varjagg/digital-modul-m/images/350d_full_cycle_original.png

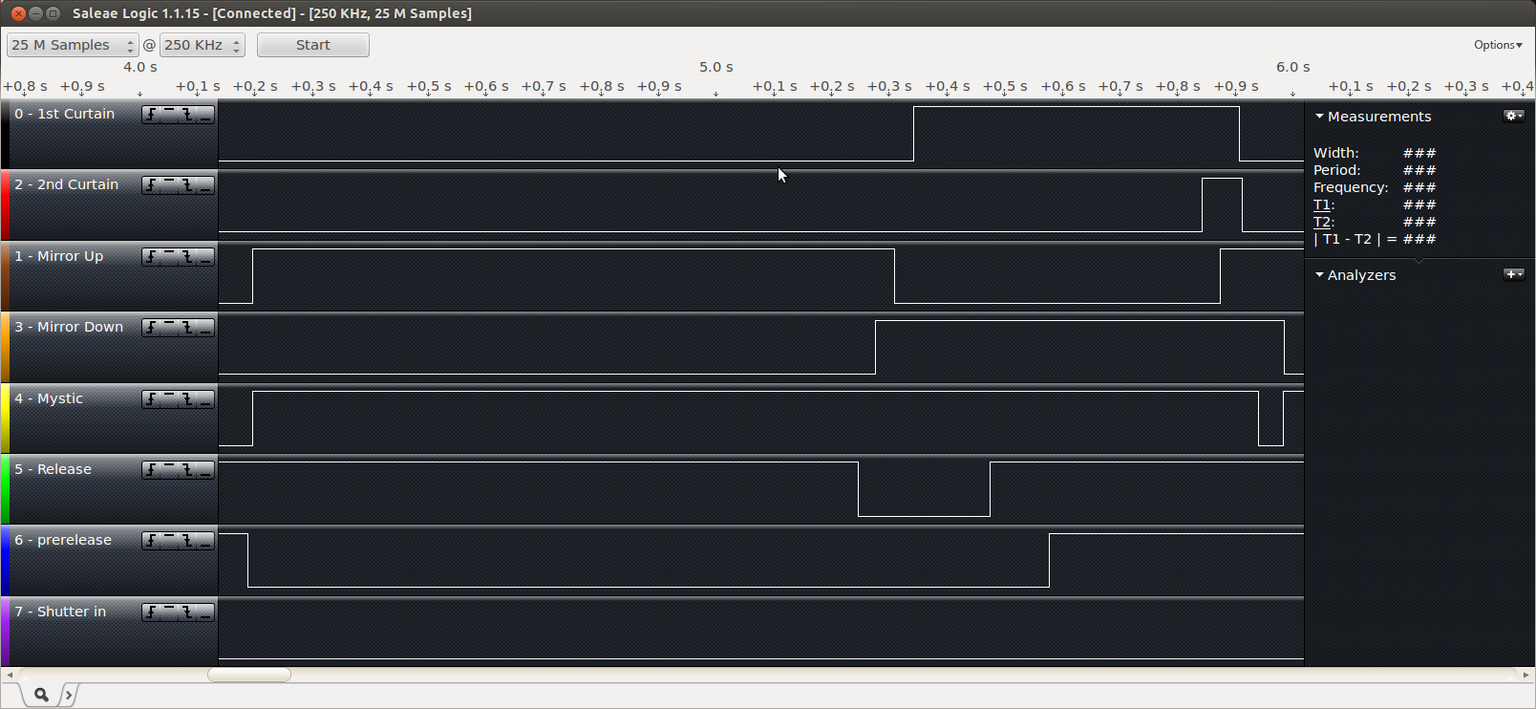
images/350d_full_cycle_original.png
