varjagg/digital-modul-m/images/actuation_uc_side.png

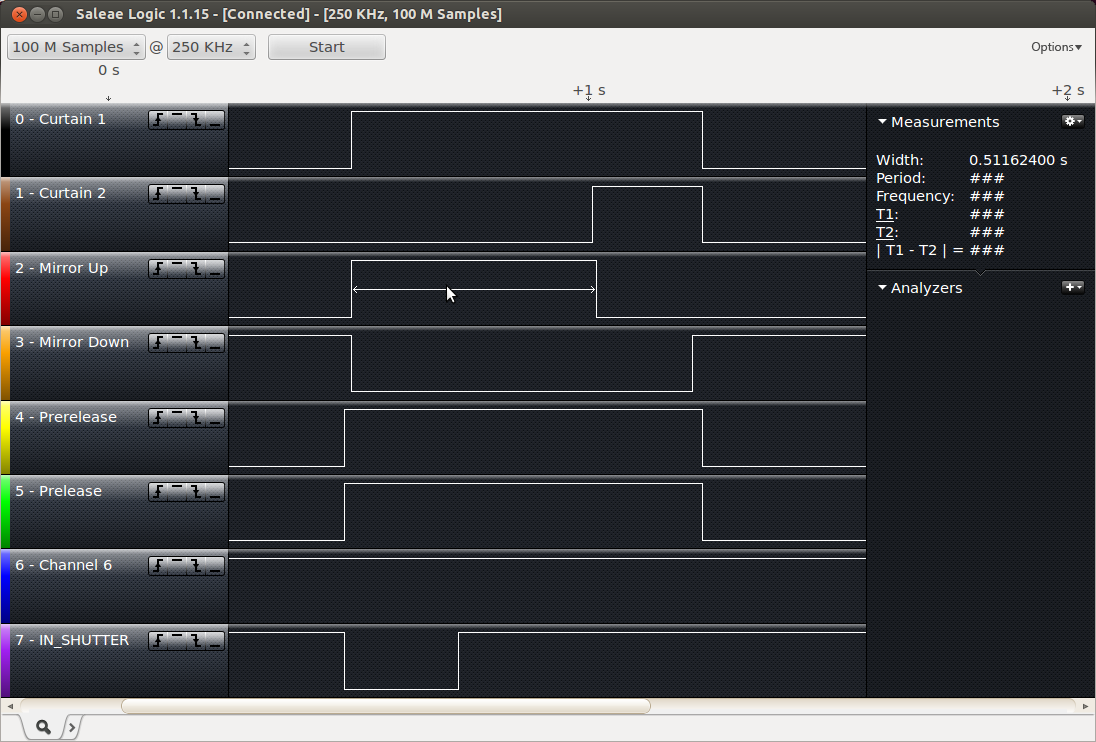
images/actuation_uc_side.png
