varjagg/digital-modul-m/images/assy/2013-04-25 13.25.53.jpg

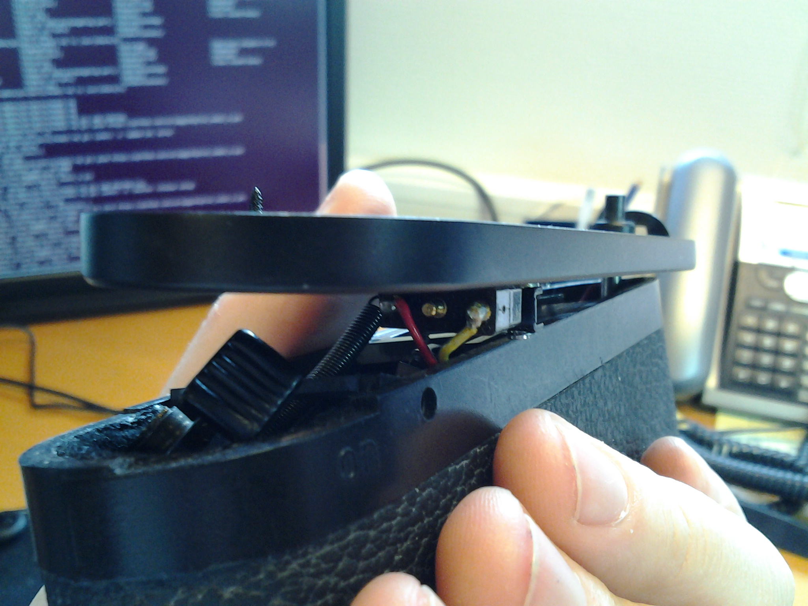
images/assy/2013-04-25 13.25.53.jpg
