varjagg/digital-modul-m/images/assy/2013-04-25 13.26.48.jpg

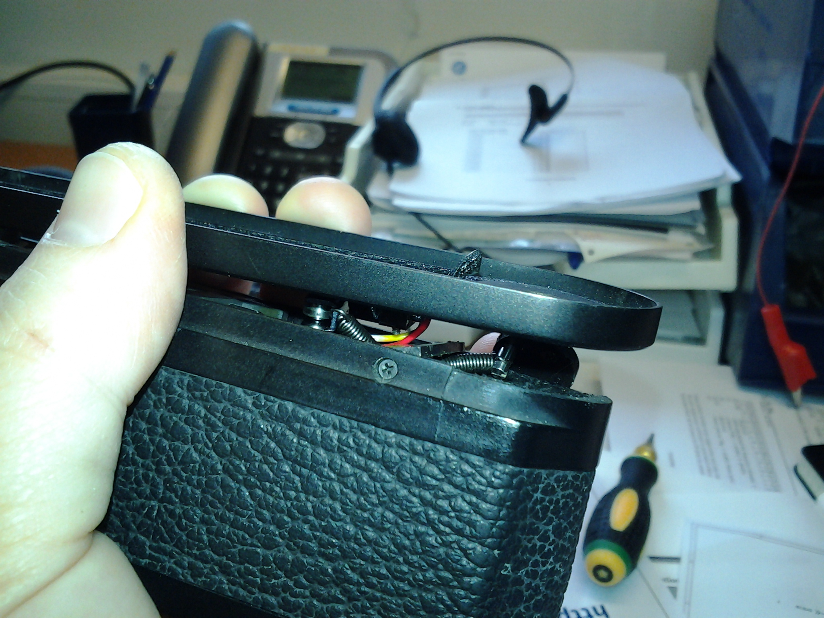
images/assy/2013-04-25 13.26.48.jpg
