varjagg/digital-modul-m/images/assy/2013-04-25 13.37.47.jpg

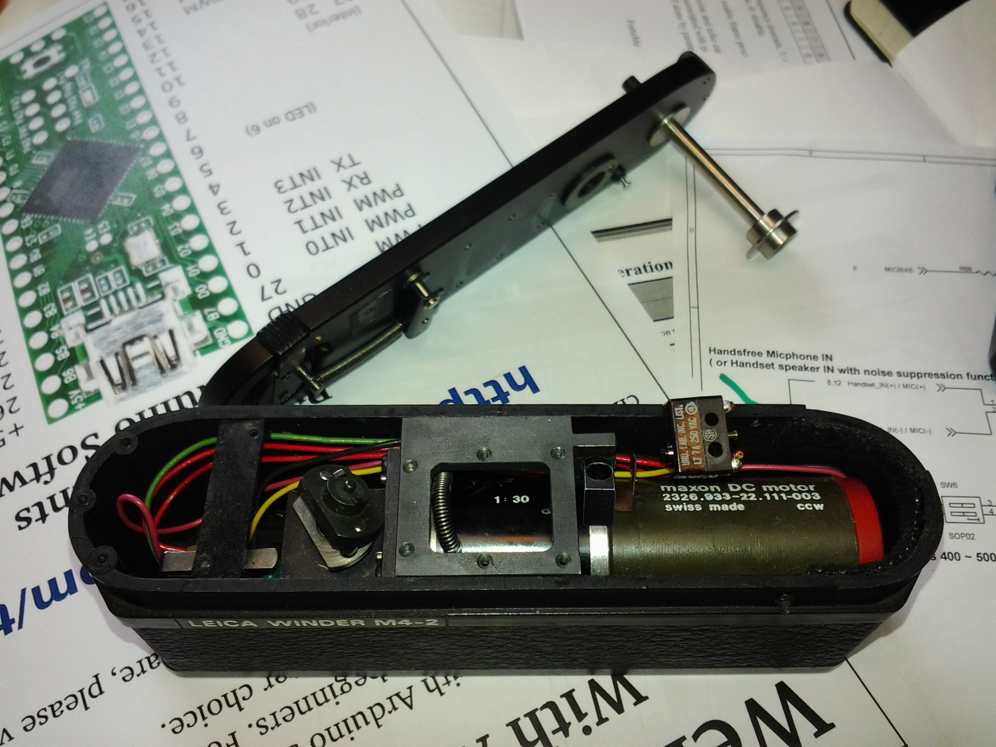
images/assy/2013-04-25 13.37.47.jpg
