varjagg/digital-modul-m/images/assy/2013-04-25 15.04.17.jpg

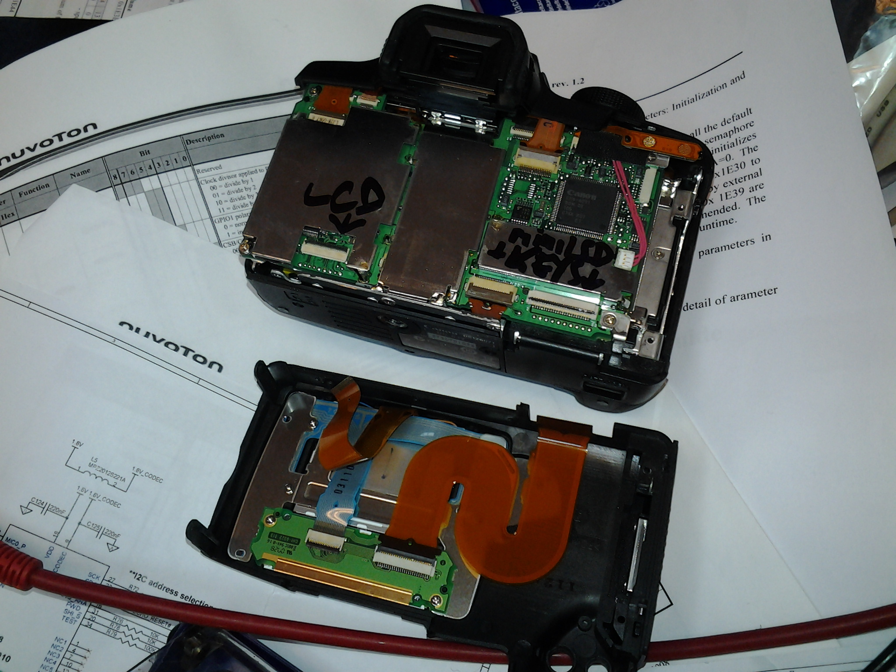
images/assy/2013-04-25 15.04.17.jpg
