varjagg/digital-modul-m/images/assy/2013-04-26 10.56.45.jpg

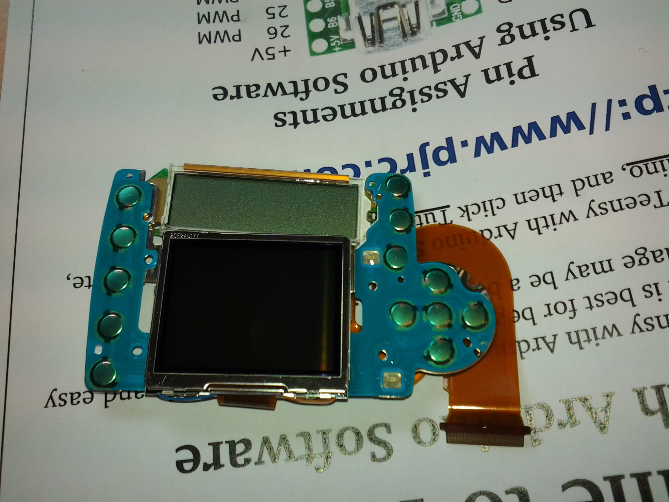
images/assy/2013-04-26 10.56.45.jpg
