varjagg/digital-modul-m/images/assy/2013-04-26 14.56.13.jpg

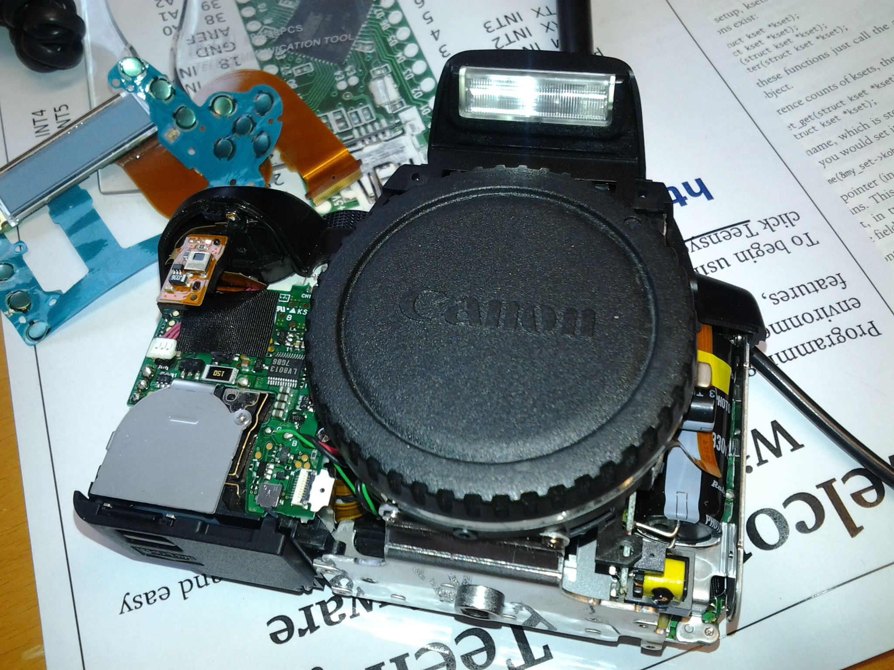
images/assy/2013-04-26 14.56.13.jpg
