varjagg/digital-modul-m/images/assy/2013-04-30 14.38.24.jpg

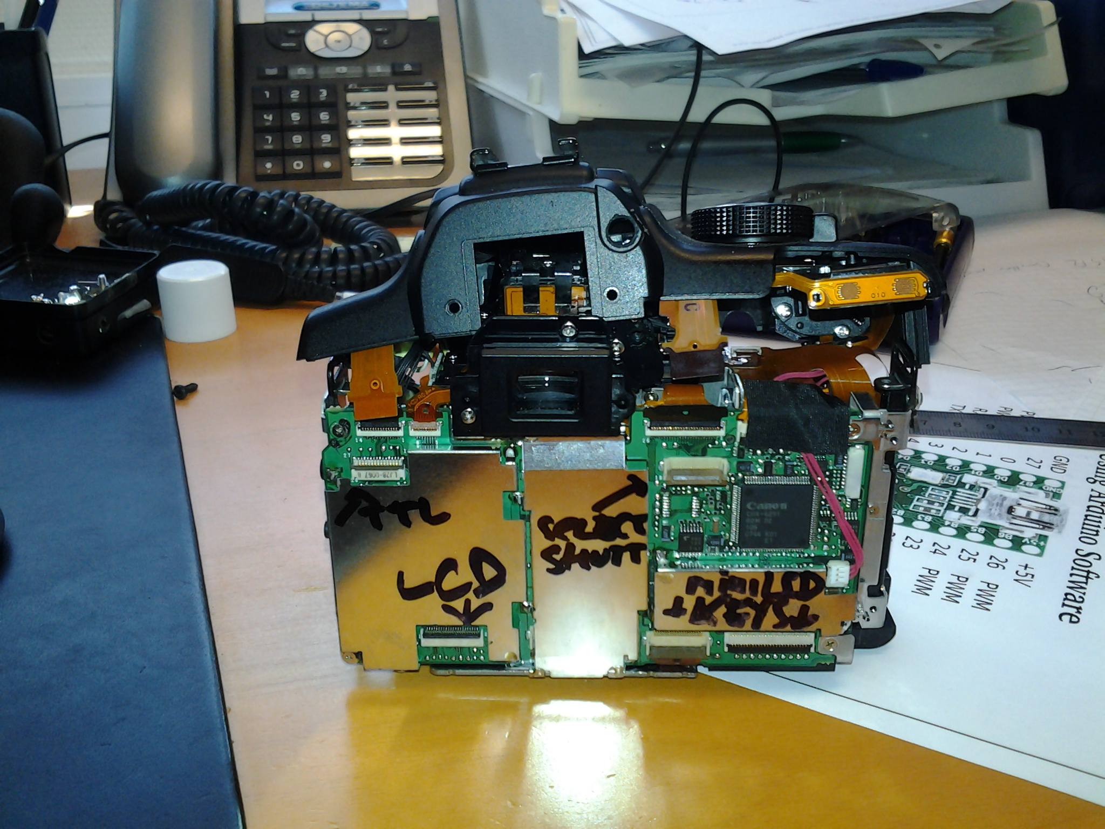
images/assy/2013-04-30 14.38.24.jpg
