varjagg/digital-modul-m/images/assy/2013-04-30 14.41.12.jpg

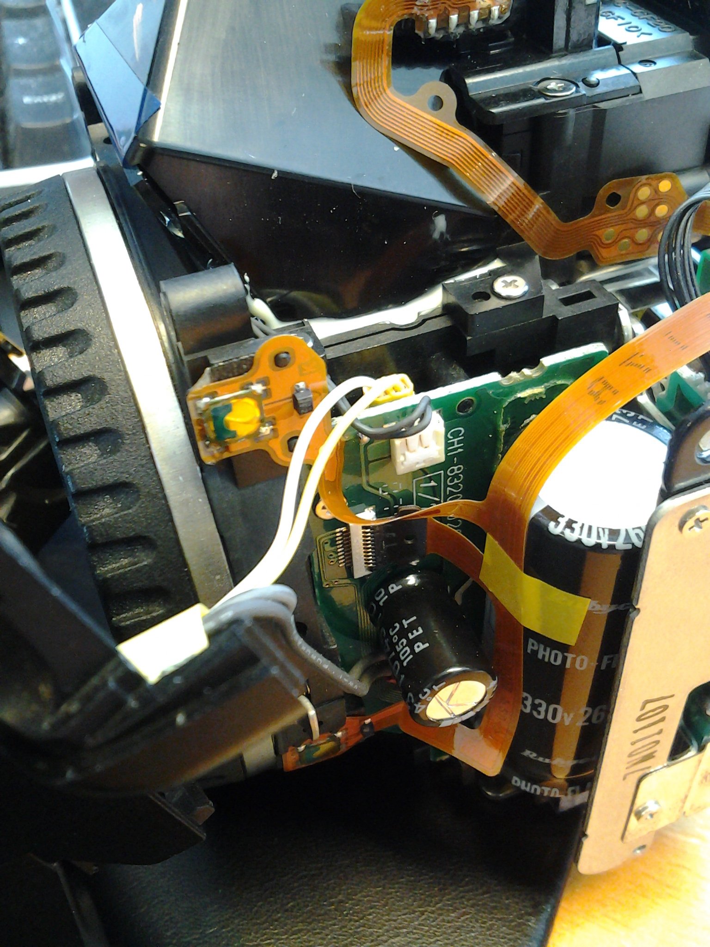
images/assy/2013-04-30 14.41.12.jpg
