varjagg/digital-modul-m/images/assy/2013-04-30 15.58.13.jpg

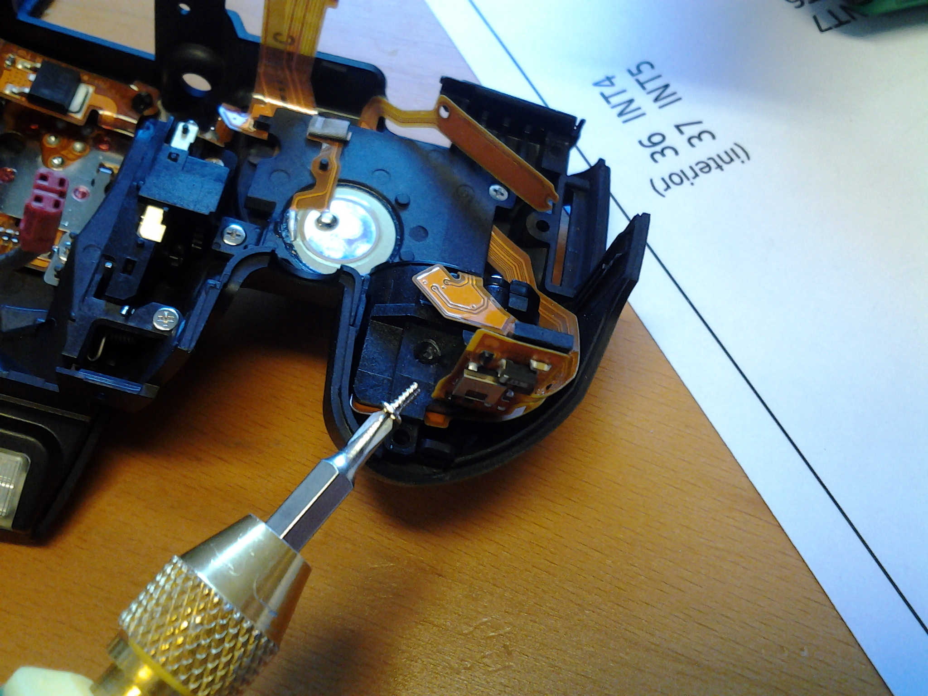
images/assy/2013-04-30 15.58.13.jpg
