varjagg/digital-modul-m/images/assy/2013-04-30 16.00.38.jpg

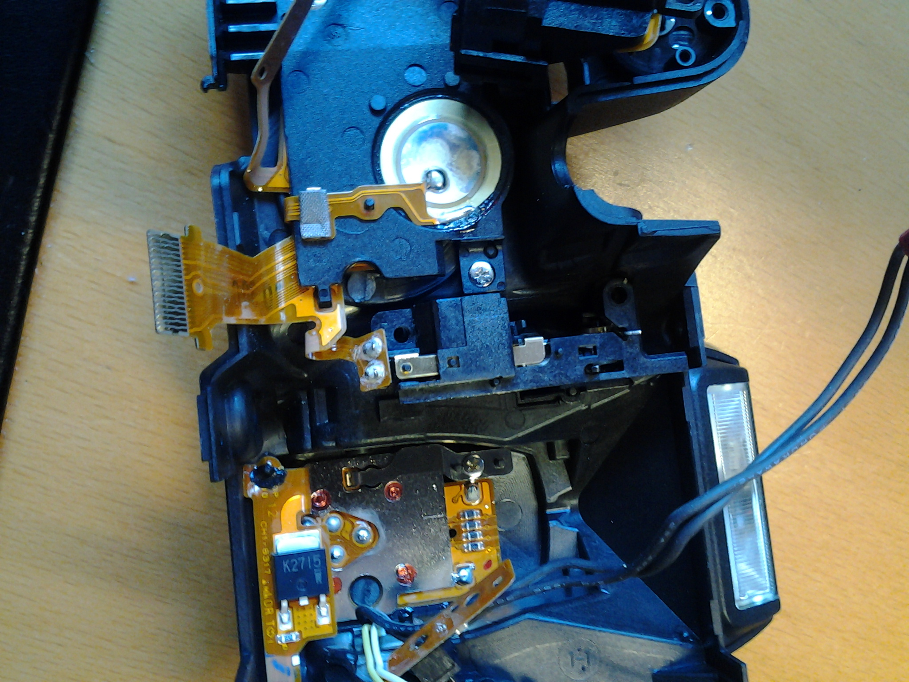
images/assy/2013-04-30 16.00.38.jpg
