varjagg/digital-modul-m/images/assy/2013-05-02 13.31.28.jpg

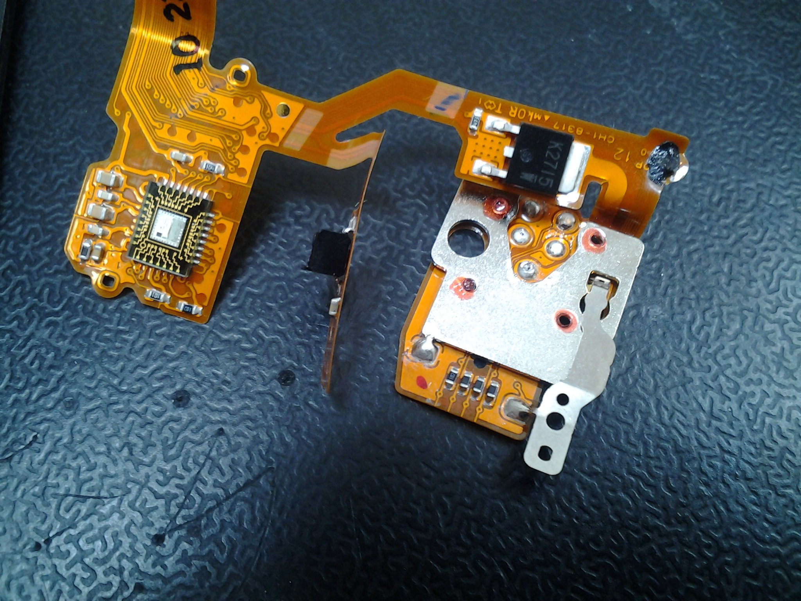
images/assy/2013-05-02 13.31.28.jpg
