varjagg/digital-modul-m/images/assy/2013-05-03 12.45.25.jpg

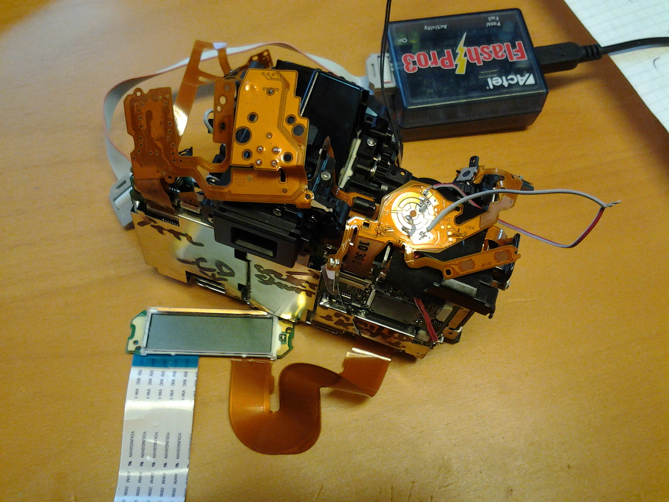
images/assy/2013-05-03 12.45.25.jpg
