varjagg/digital-modul-m/images/assy/2013-05-06 17.41.58.jpg

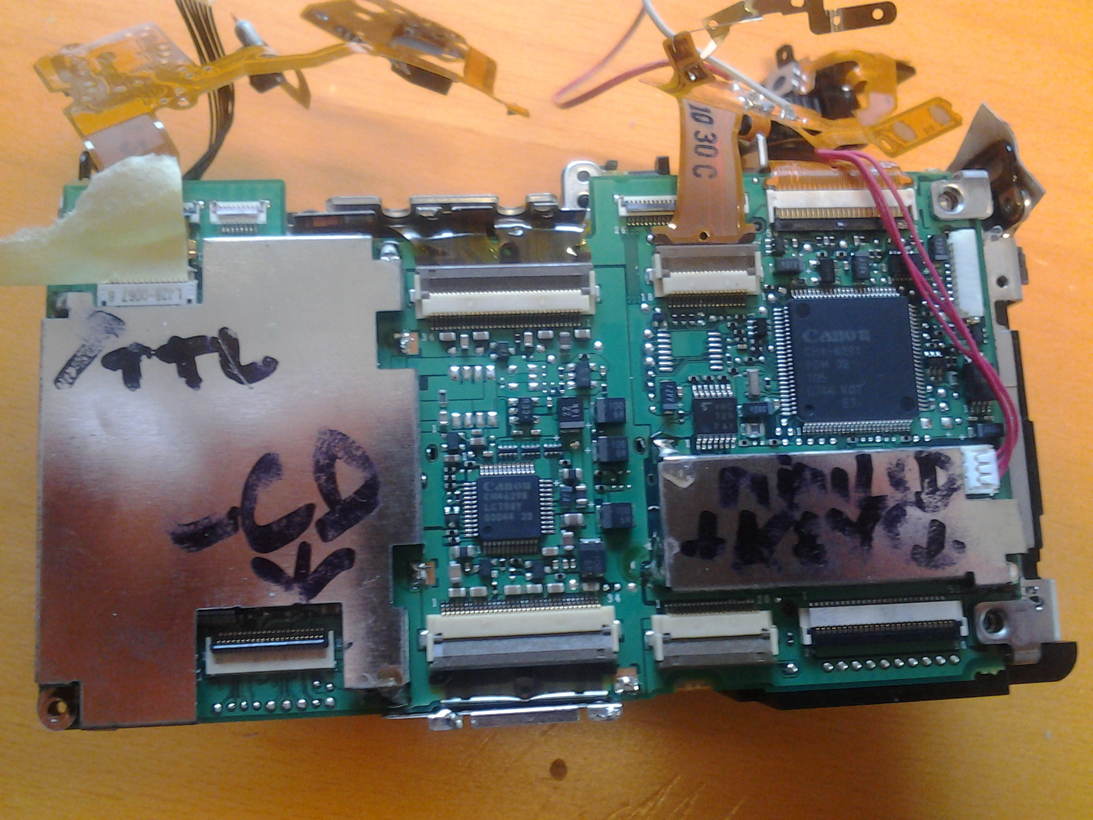
images/assy/2013-05-06 17.41.58.jpg
