varjagg/digital-modul-m/images/assy/2013-05-06 17.49.36.jpg

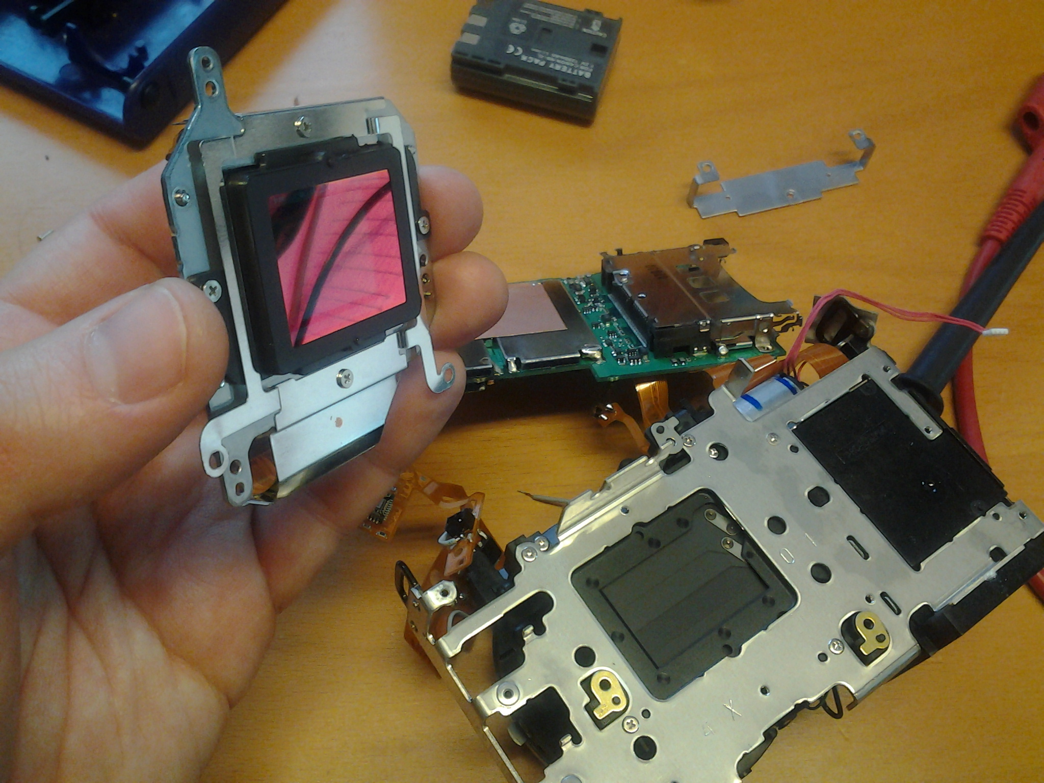
images/assy/2013-05-06 17.49.36.jpg
