varjagg/digital-modul-m/images/assy/2013-05-07 17.15.51.jpg

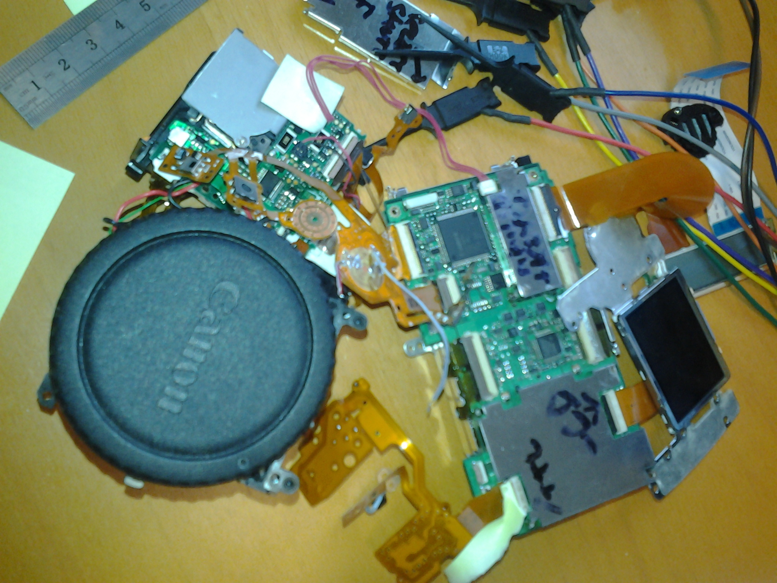
images/assy/2013-05-07 17.15.51.jpg
