varjagg/digital-modul-m/images/assy/2013-12-18 17.05.55.jpg

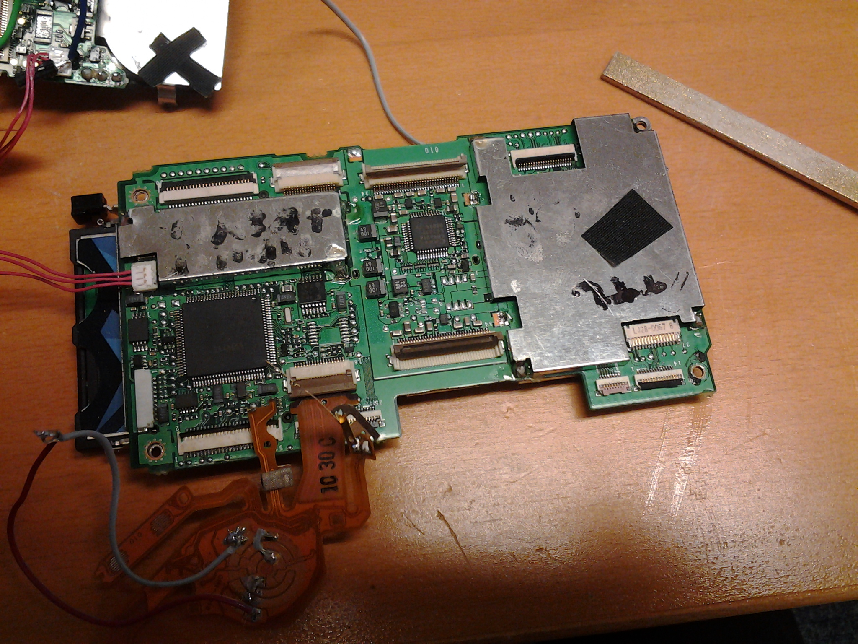
images/assy/2013-12-18 17.05.55.jpg
