varjagg/digital-modul-m/images/assy/2013-12-19 19.09.14.jpg

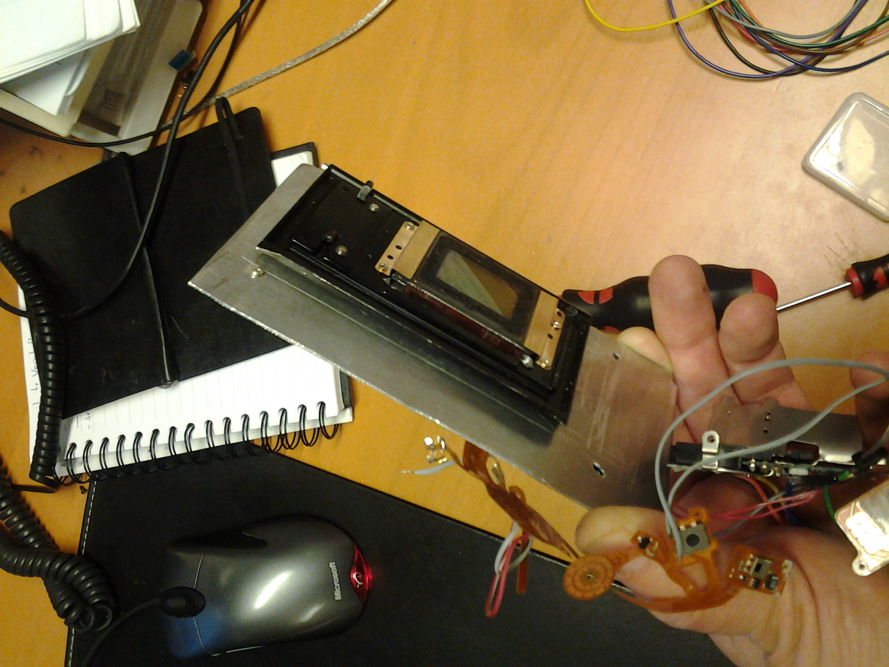
images/assy/2013-12-19 19.09.14.jpg
