varjagg/digital-modul-m/images/assy/2013-12-20 17.21.03.jpg

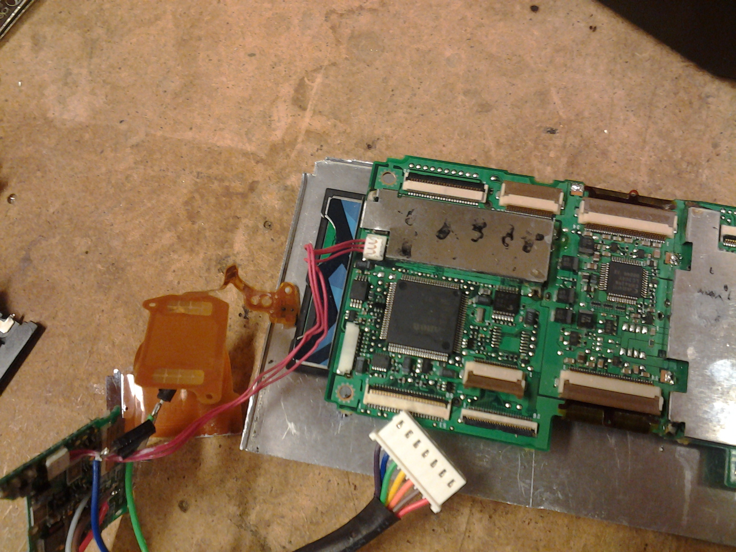
images/assy/2013-12-20 17.21.03.jpg
