varjagg/digital-modul-m/images/assy/2013-12-20 17.26.51.jpg

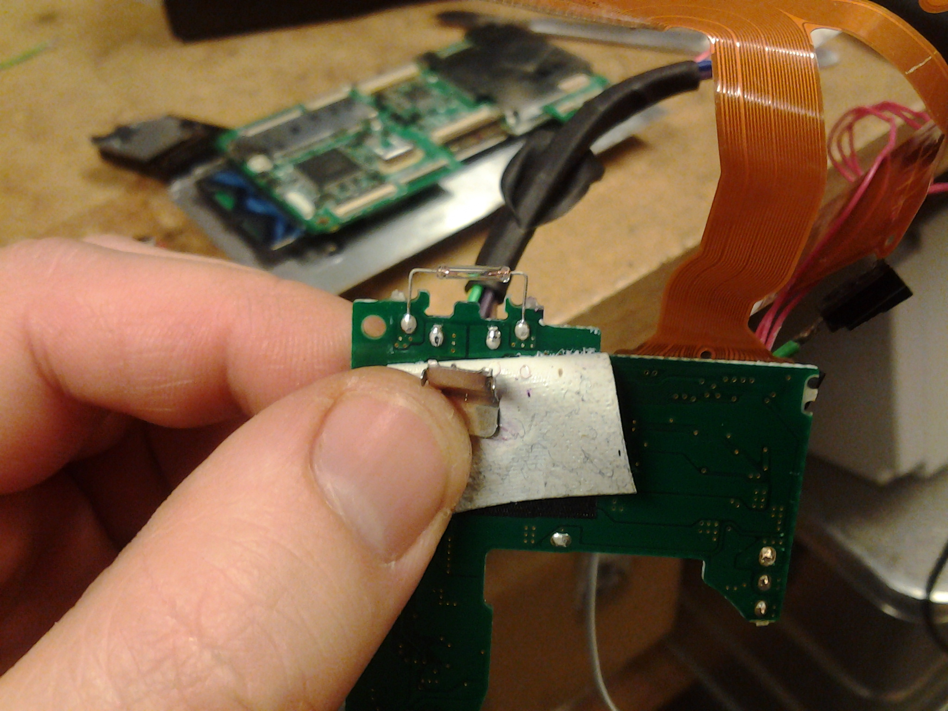
images/assy/2013-12-20 17.26.51.jpg
