varjagg/digital-modul-m/images/assy/2013-12-20 18.12.20.jpg

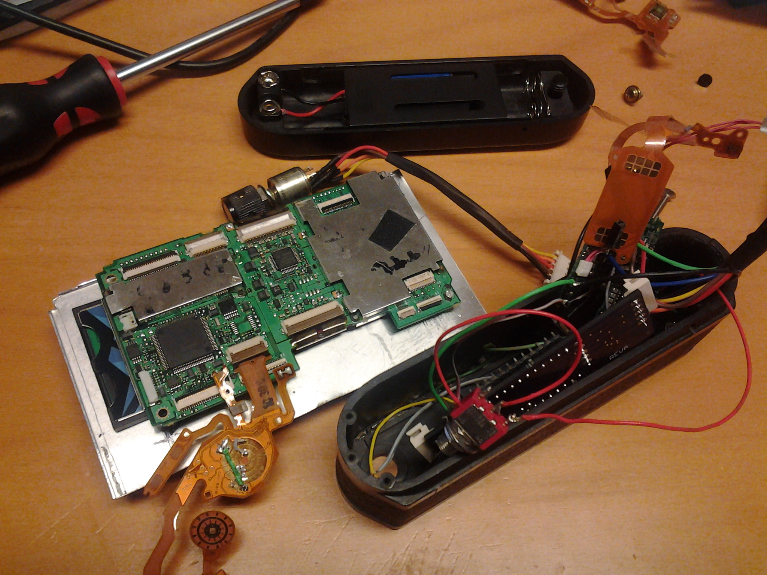
images/assy/2013-12-20 18.12.20.jpg
