varjagg/digital-modul-m/images/assy/2014-01-19 21.56.09.jpg

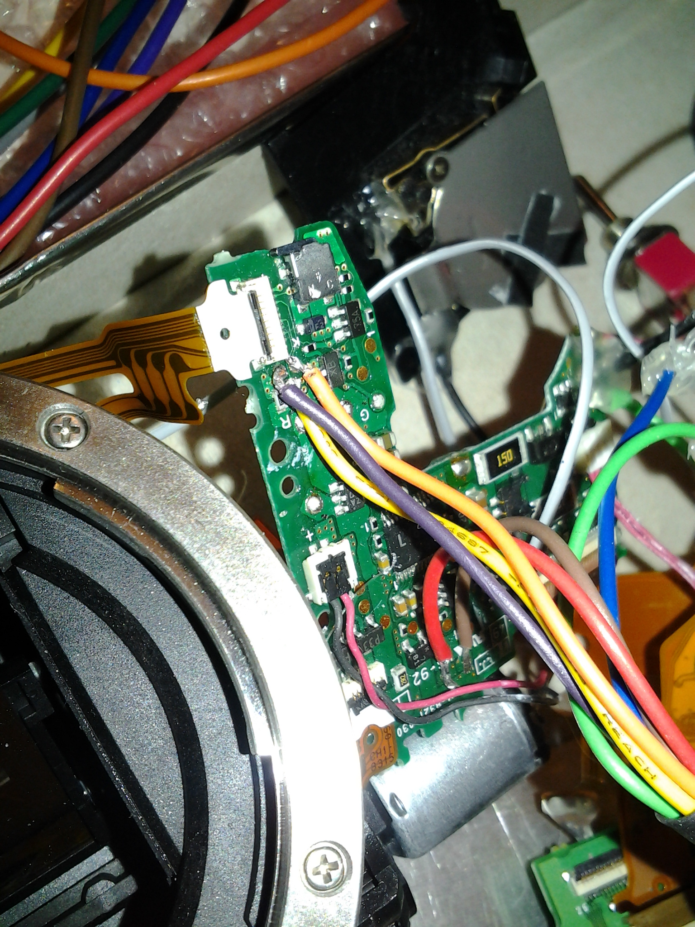
images/assy/2014-01-19 21.56.09.jpg
