varjagg/digital-modul-m/images/assy/2014-03-30 21.18.12.jpg

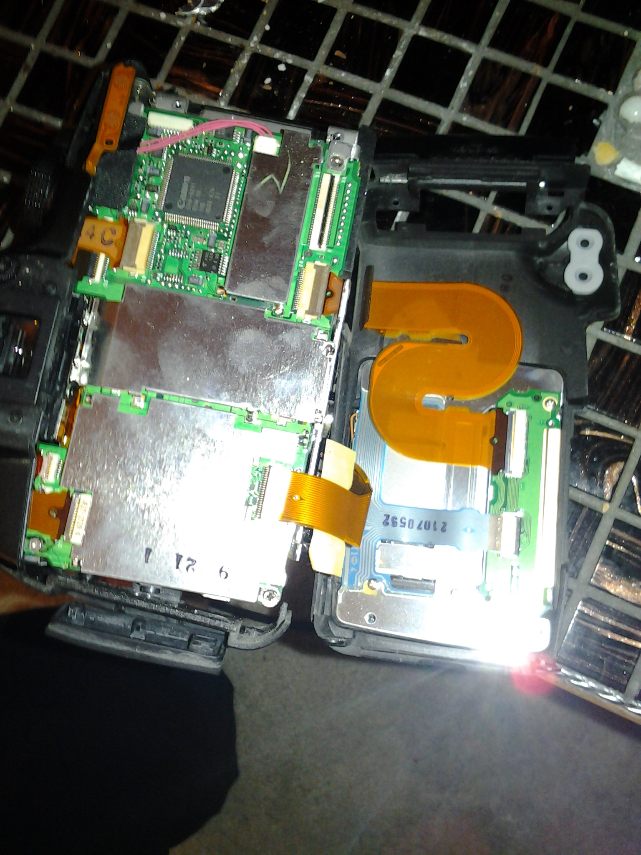
images/assy/2014-03-30 21.18.12.jpg
