varjagg/digital-modul-m/images/assy/2014-03-30 21.30.56.jpg

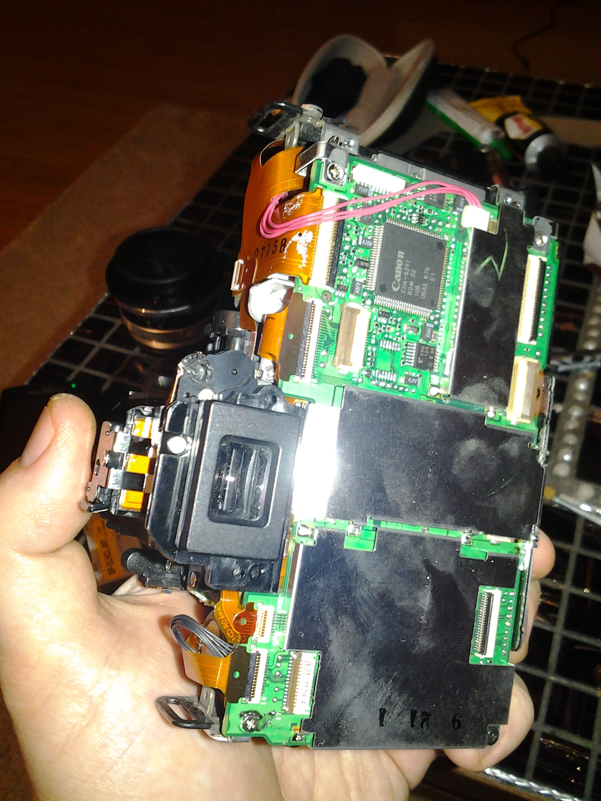
images/assy/2014-03-30 21.30.56.jpg
