varjagg/digital-modul-m/images/assy/2014-05-11 17.10.10.jpg

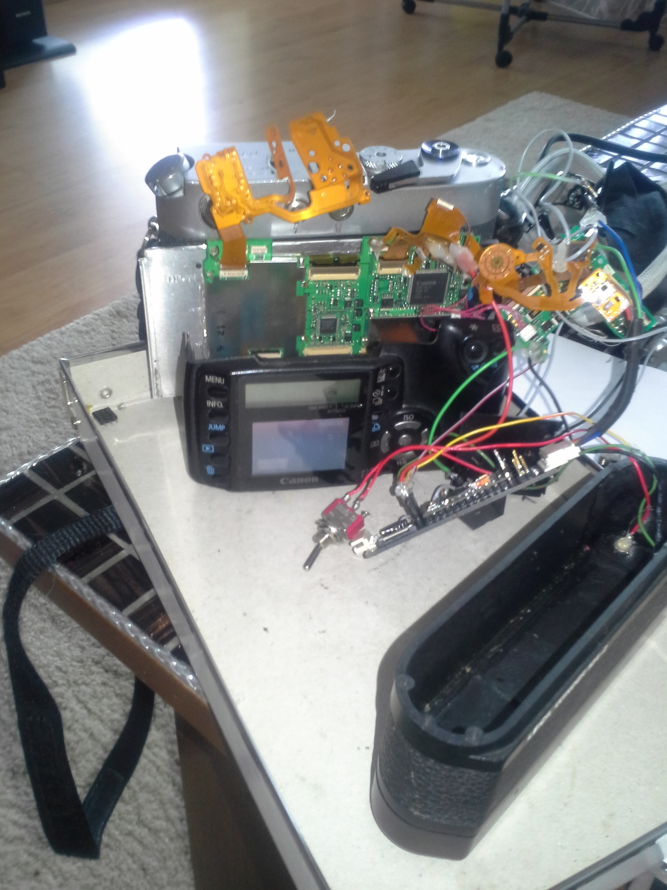
images/assy/2014-05-11 17.10.10.jpg
