varjagg/digital-modul-m/images/assy/2014-05-12 11.59.01.jpg

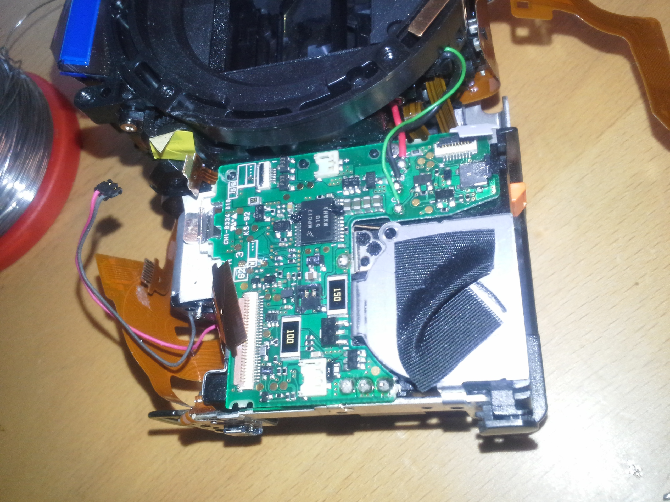
images/assy/2014-05-12 11.59.01.jpg
