varjagg/digital-modul-m/images/assy/2014-05-12 22.17.48.jpg

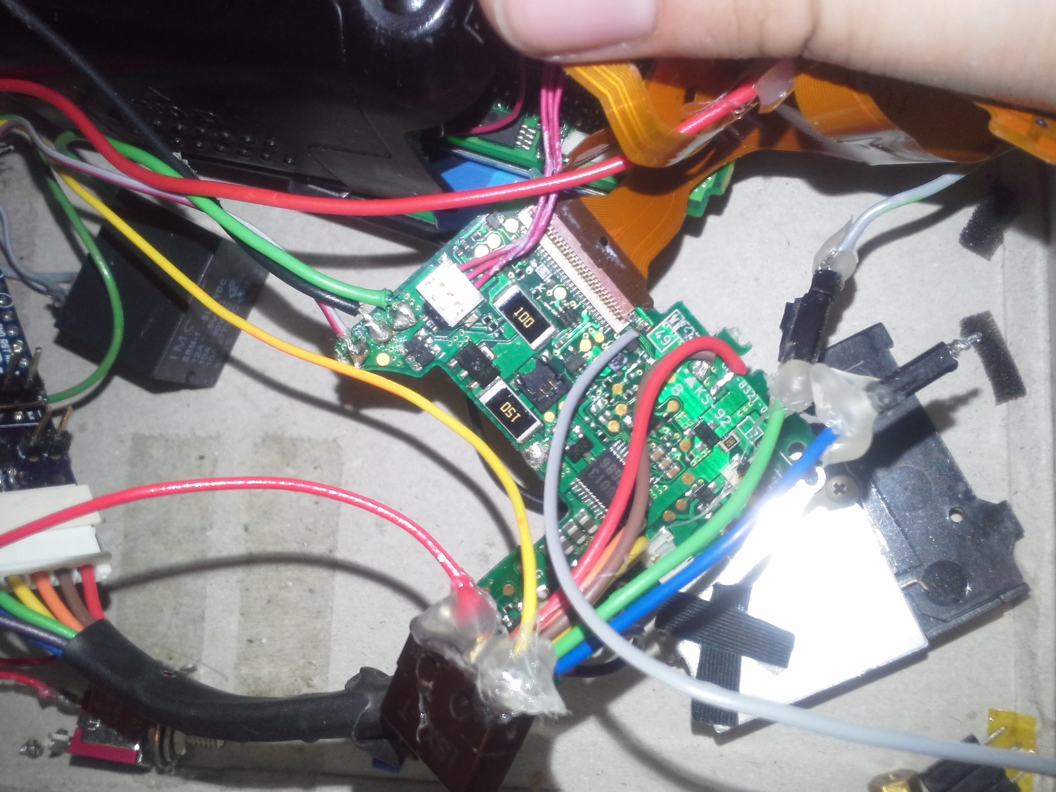
images/assy/2014-05-12 22.17.48.jpg
