varjagg/digital-modul-m/images/assy/2014-05-29 17.47.46.jpg

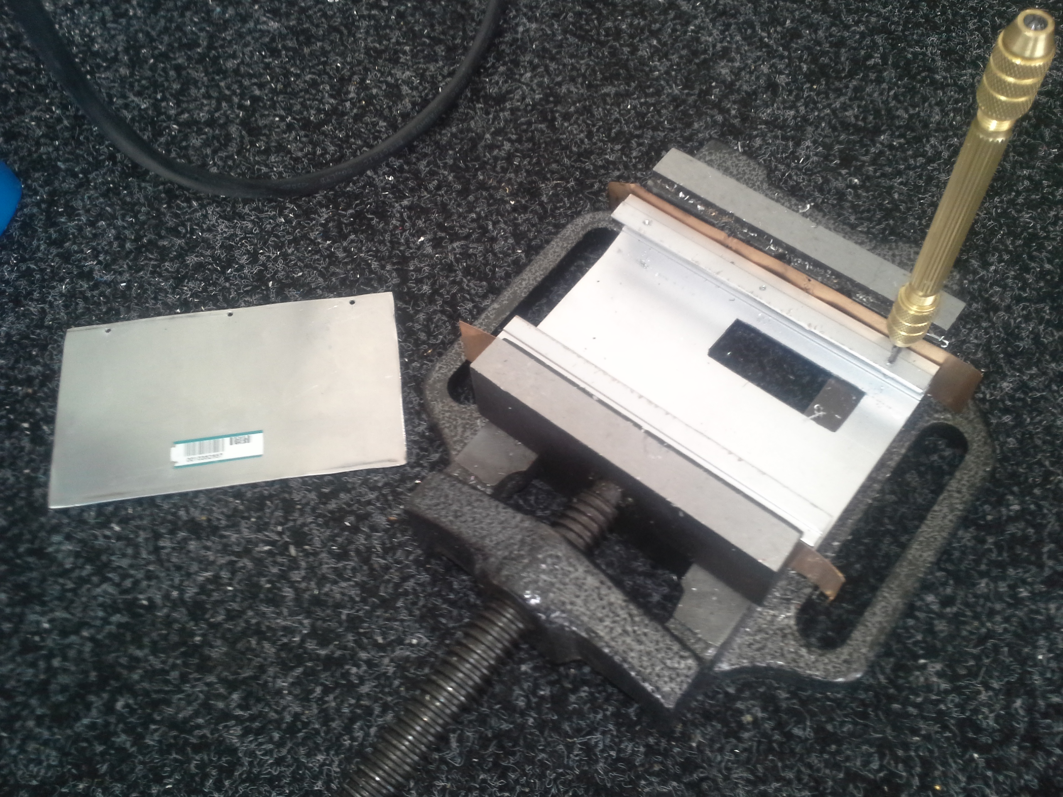
images/assy/2014-05-29 17.47.46.jpg
