varjagg/digital-modul-m/images/assy/2014-05-29 18.29.52.jpg

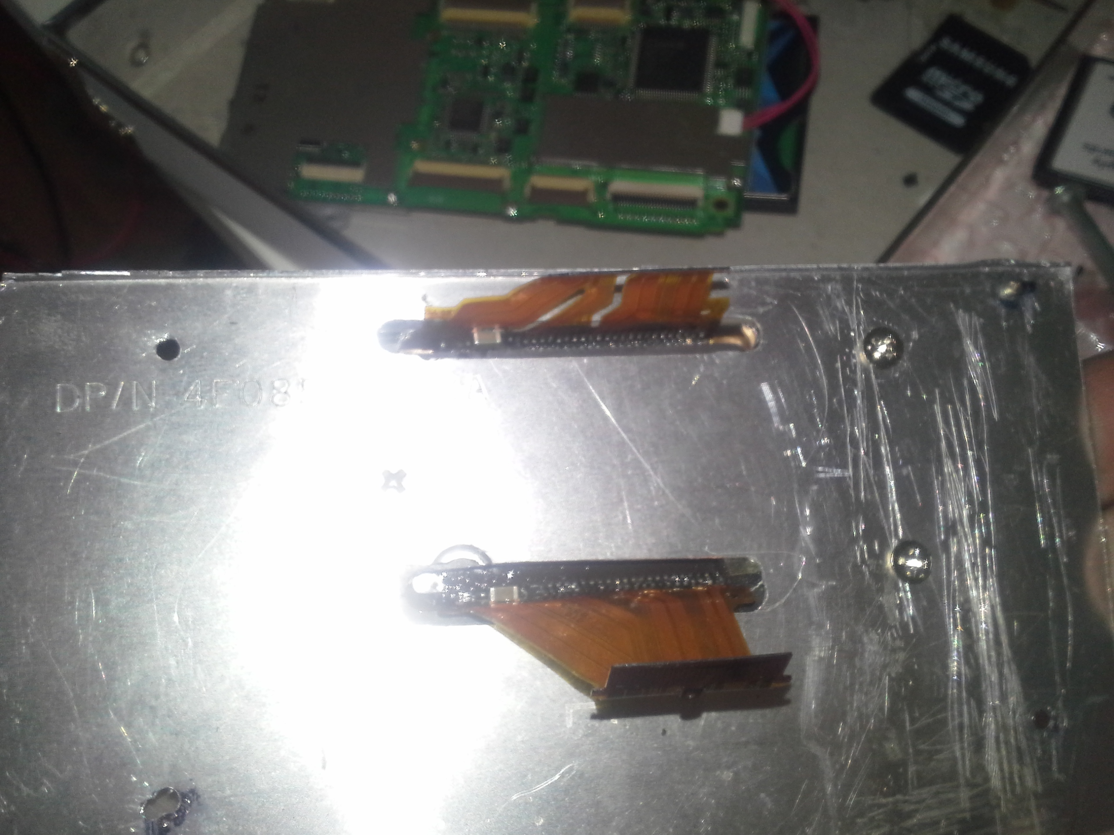
images/assy/2014-05-29 18.29.52.jpg
