varjagg/digital-modul-m/images/assy/2014-05-29 19.08.57.jpg

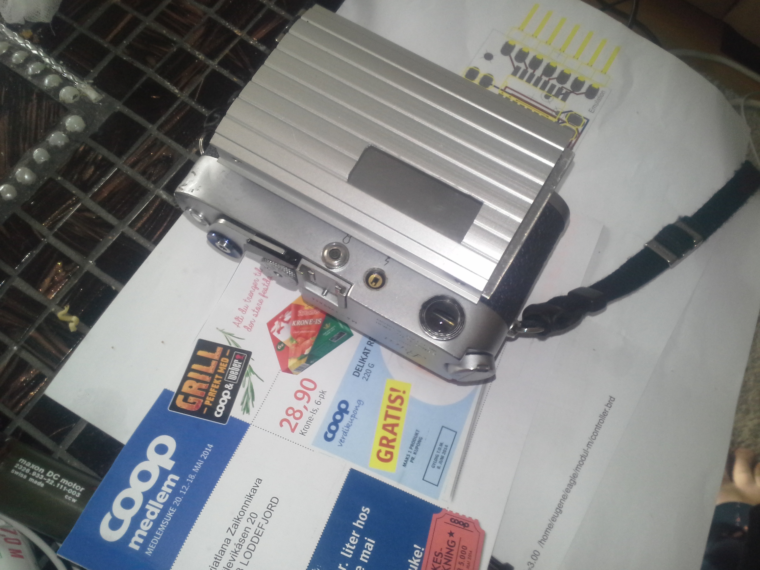
images/assy/2014-05-29 19.08.57.jpg
