varjagg/digital-modul-m/images/assy/2014-07-13 12.51.36.jpg

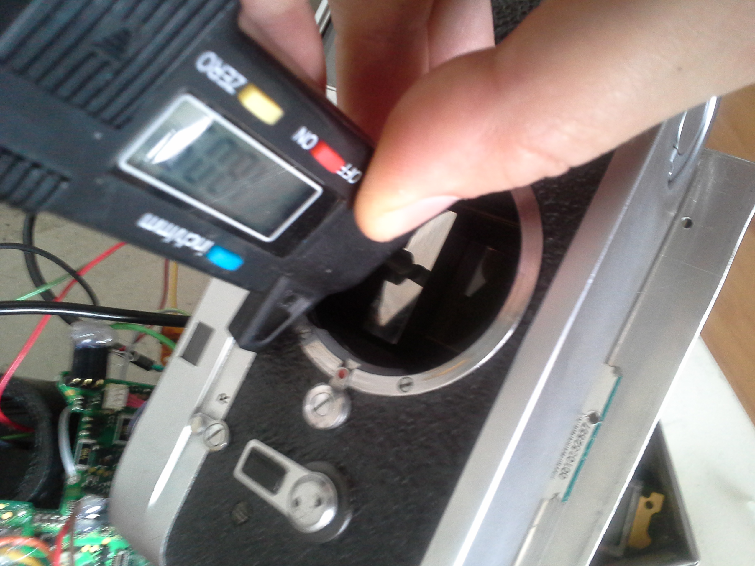
images/assy/2014-07-13 12.51.36.jpg
