varjagg/digital-modul-m/images/assy/2014-07-13 13.20.39.jpg

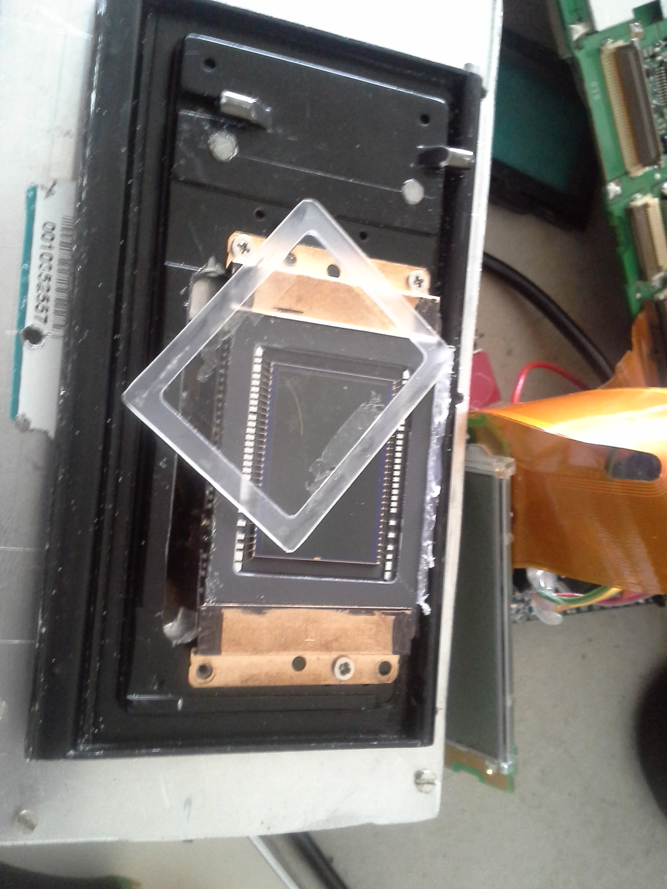
images/assy/2014-07-13 13.20.39.jpg
