varjagg/digital-modul-m/images/assy/2014-07-13 13.47.36.jpg

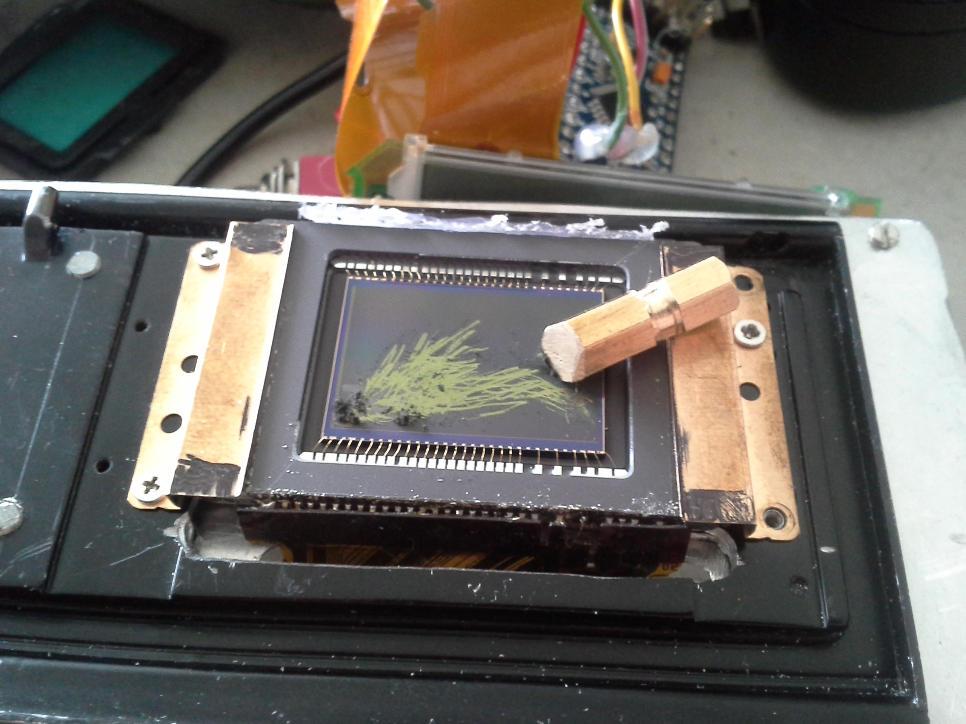
images/assy/2014-07-13 13.47.36.jpg
