varjagg/digital-modul-m/images/assy/2014-07-16 19.50.07.jpg

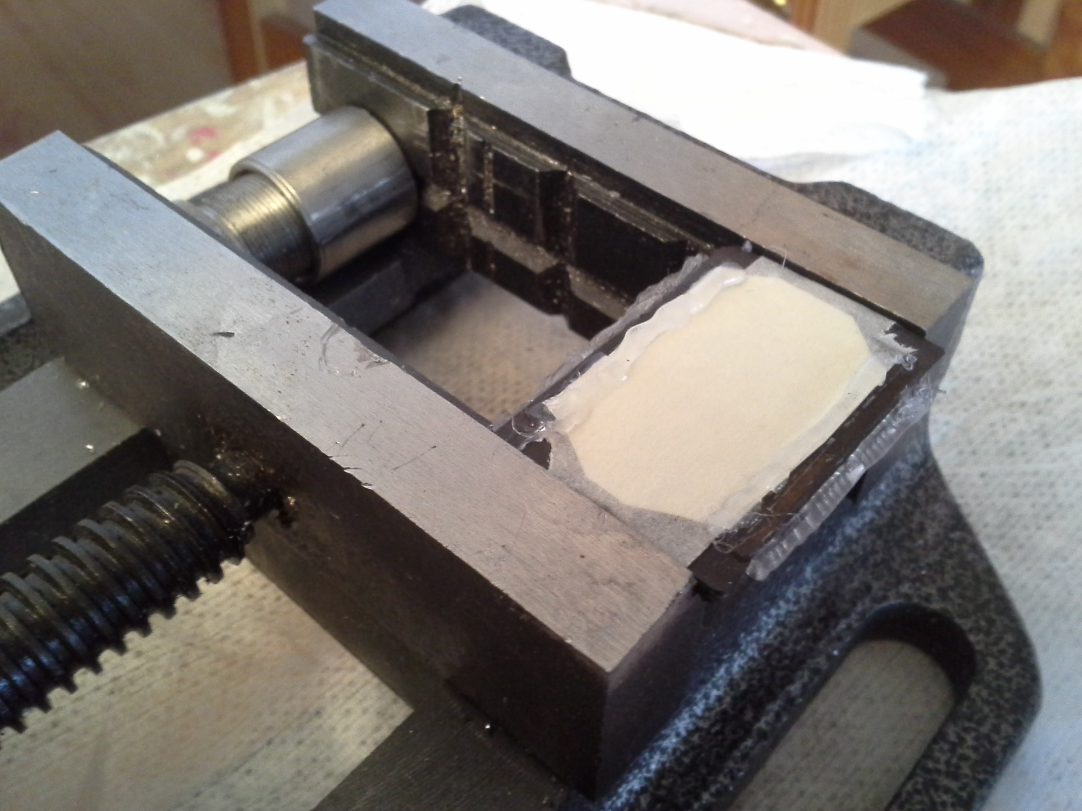
images/assy/2014-07-16 19.50.07.jpg
