varjagg/digital-modul-m/images/assy/2014-07-16 20.57.48.jpg

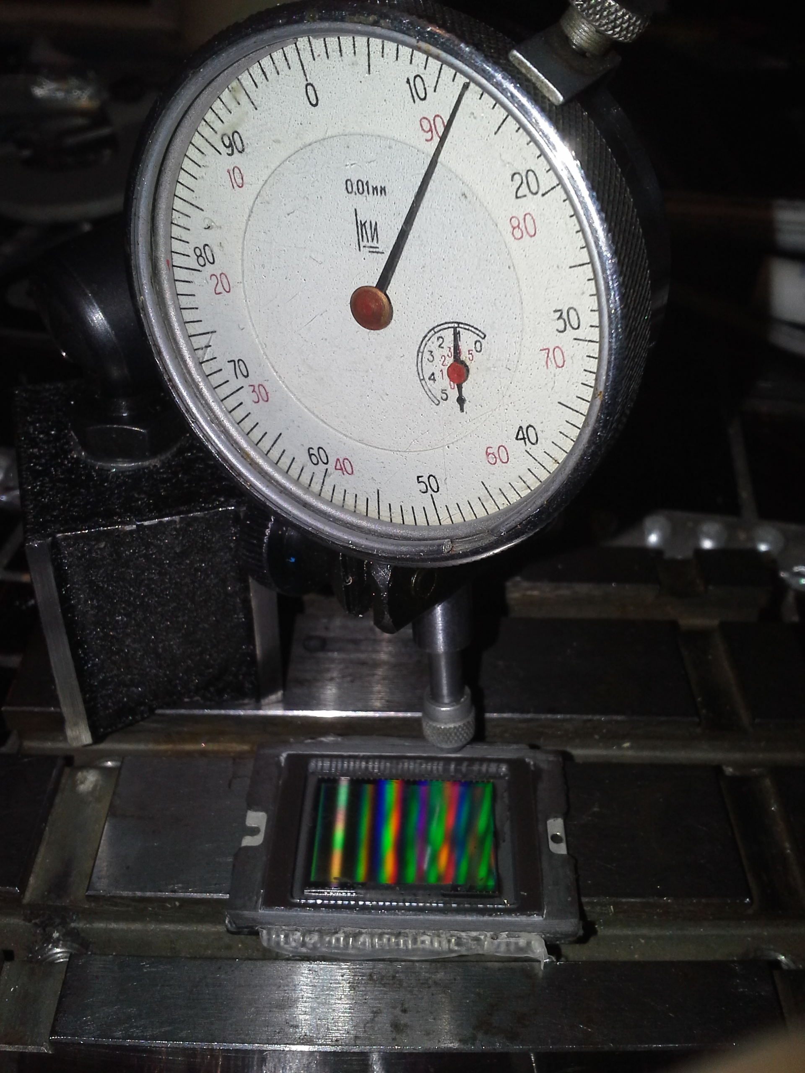
images/assy/2014-07-16 20.57.48.jpg
