varjagg/digital-modul-m/images/assy/2014-07-16 22.43.36.jpg

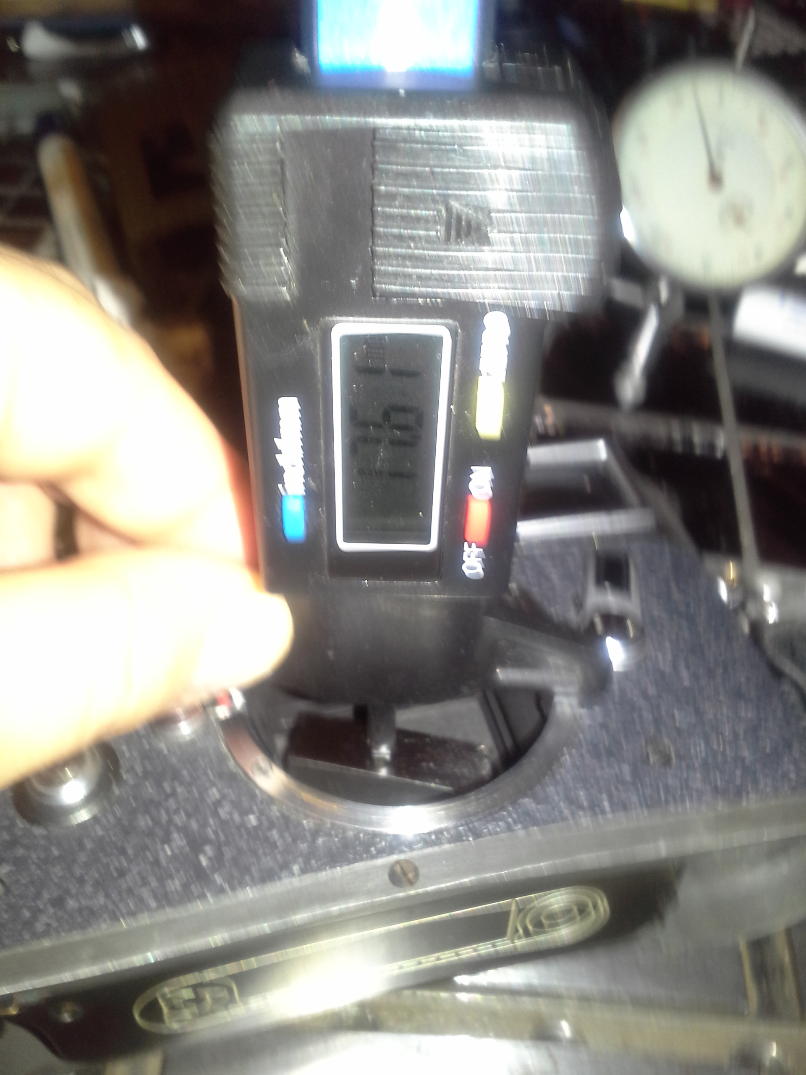
images/assy/2014-07-16 22.43.36.jpg
