varjagg/digital-modul-m/images/assy/2014-07-16 22.45.16.jpg

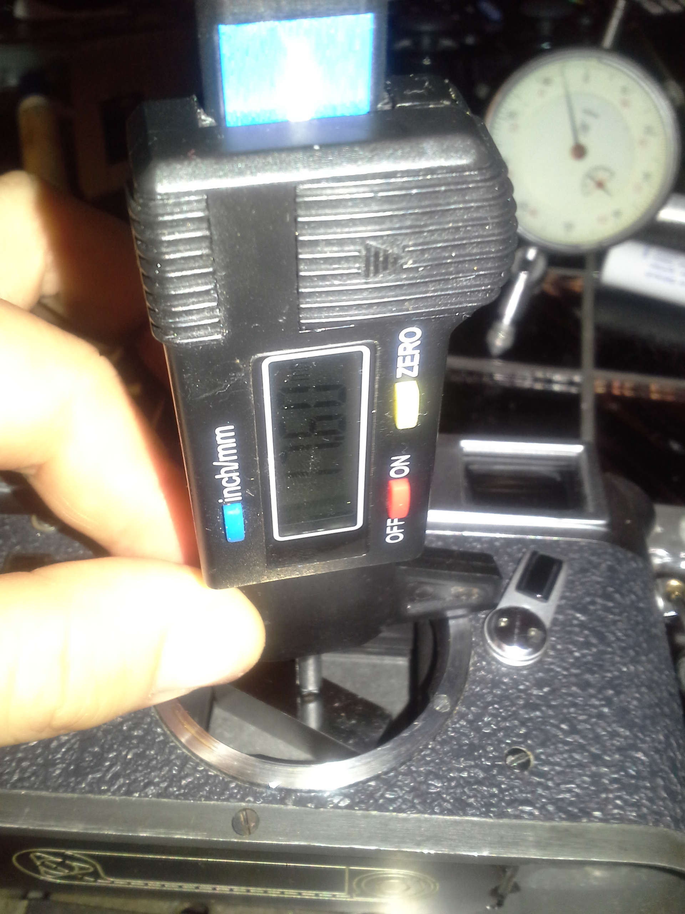
images/assy/2014-07-16 22.45.16.jpg
