varjagg/digital-modul-m/images/assy/2014-07-17 01.21.00.jpg

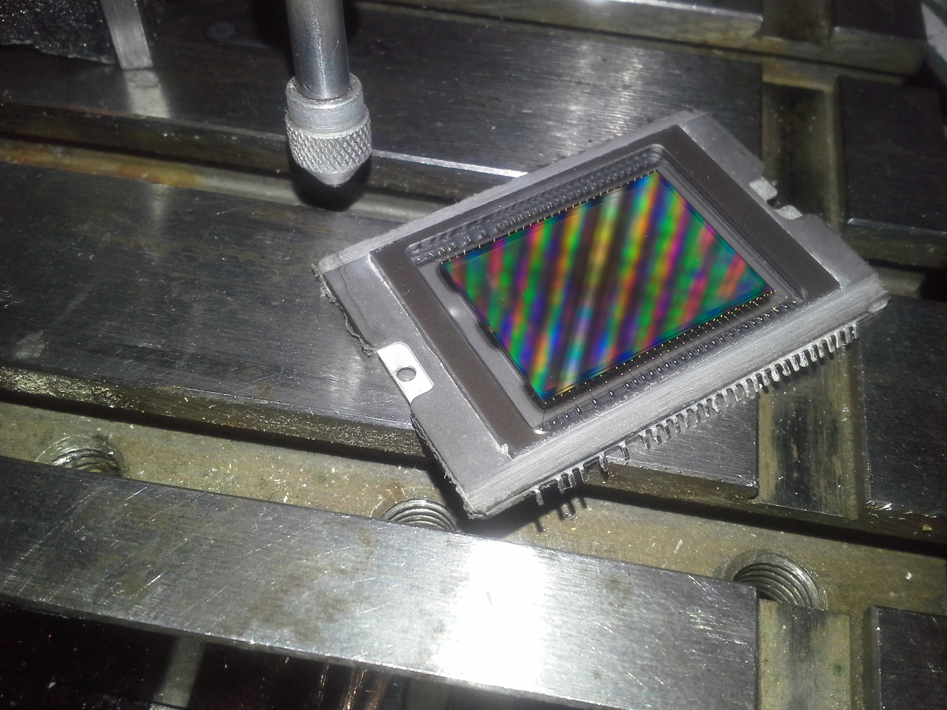
images/assy/2014-07-17 01.21.00.jpg
