varjagg/digital-modul-m/images/assy/2014-08-02 18.19.36.jpg

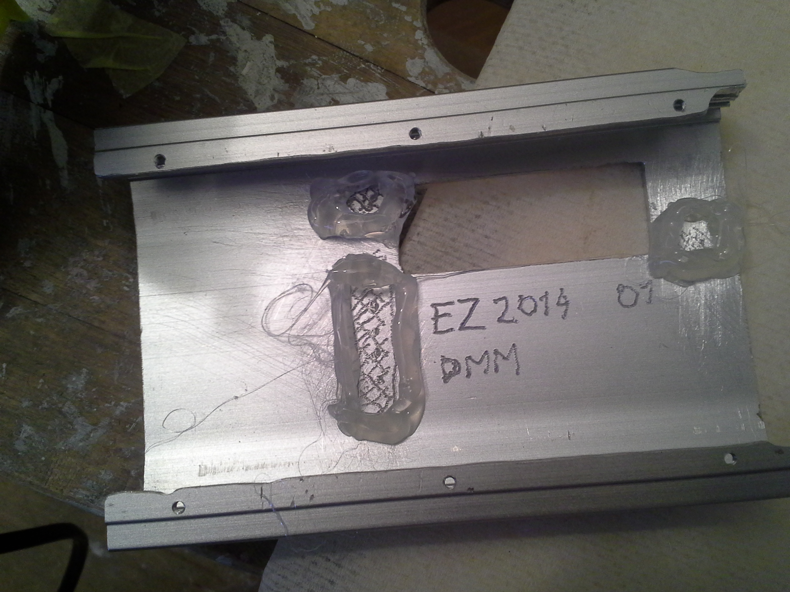
images/assy/2014-08-02 18.19.36.jpg
