varjagg/digital-modul-m/images/assy/2014-08-02 21.22.23.jpg

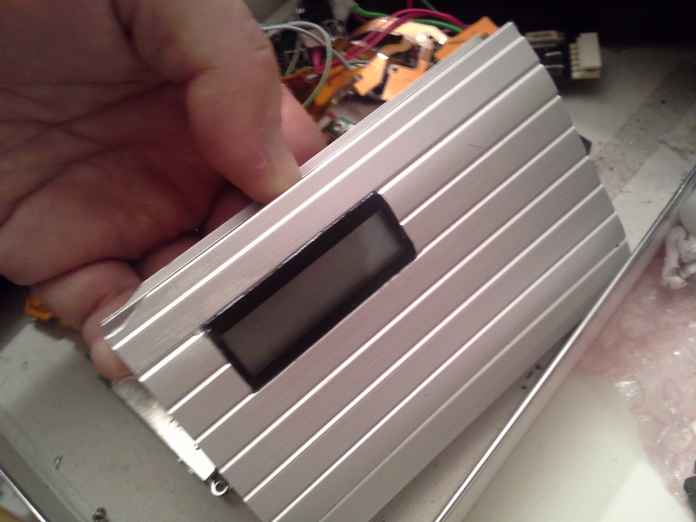
images/assy/2014-08-02 21.22.23.jpg
