varjagg/digital-modul-m/images/assy/2014-08-03 13.05.19.jpg

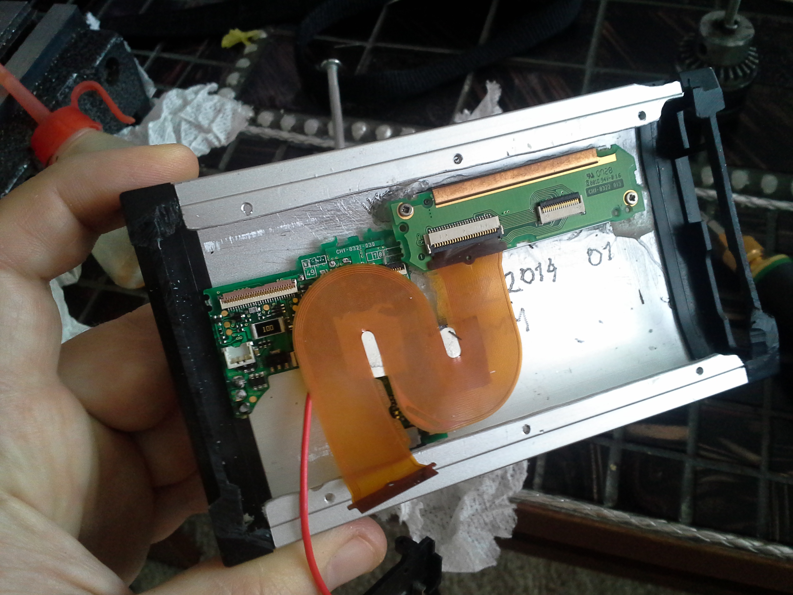
images/assy/2014-08-03 13.05.19.jpg
