varjagg/digital-modul-m/images/assy/2014-08-03 16.58.47.jpg

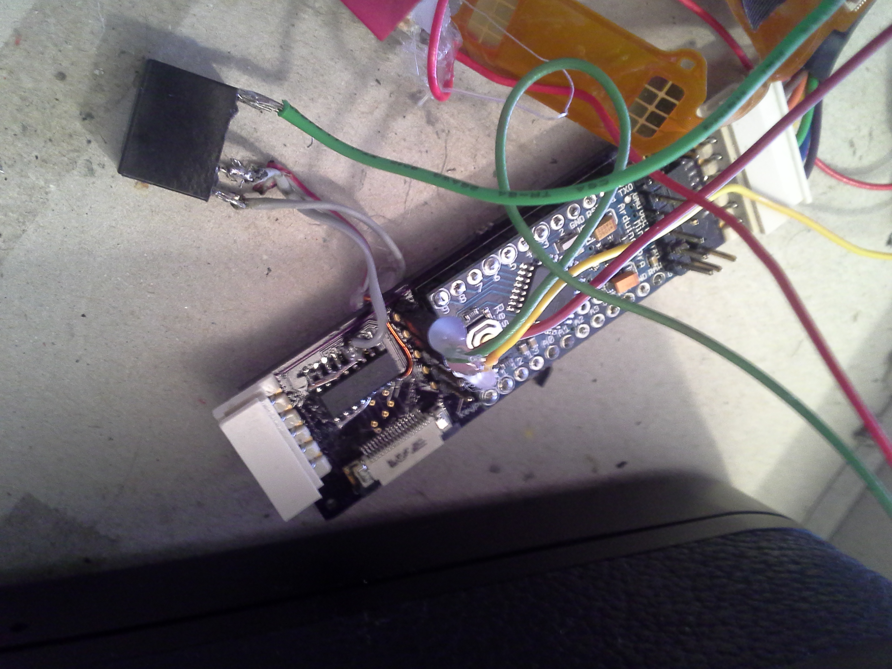
images/assy/2014-08-03 16.58.47.jpg
