varjagg/digital-modul-m/images/assy/2014-08-03 19.27.08.jpg

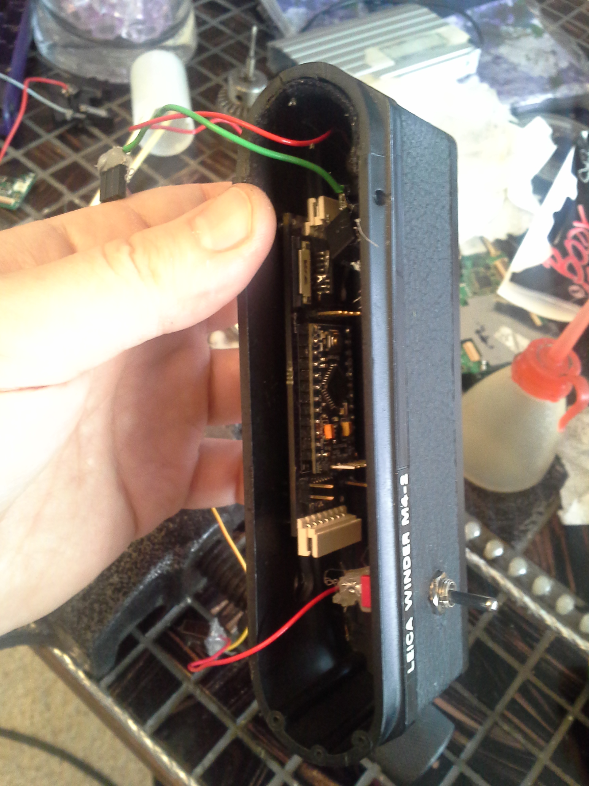
images/assy/2014-08-03 19.27.08.jpg
