varjagg/digital-modul-m/images/assy/2014-08-03 21.01.43.jpg

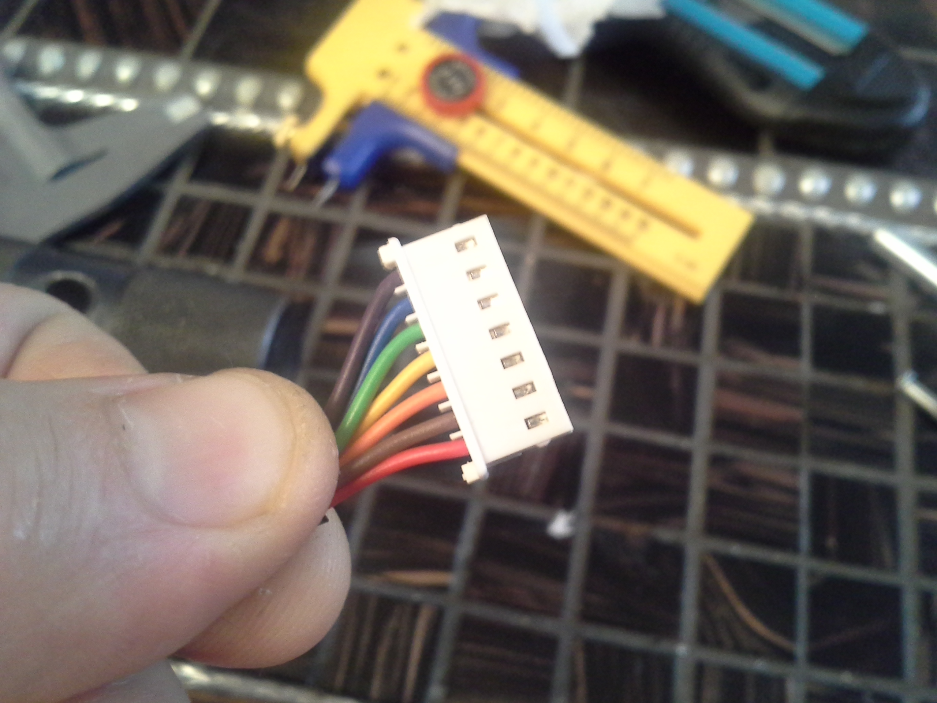
images/assy/2014-08-03 21.01.43.jpg
