varjagg/digital-modul-m/images/assy/2014-08-03 21.07.59.jpg

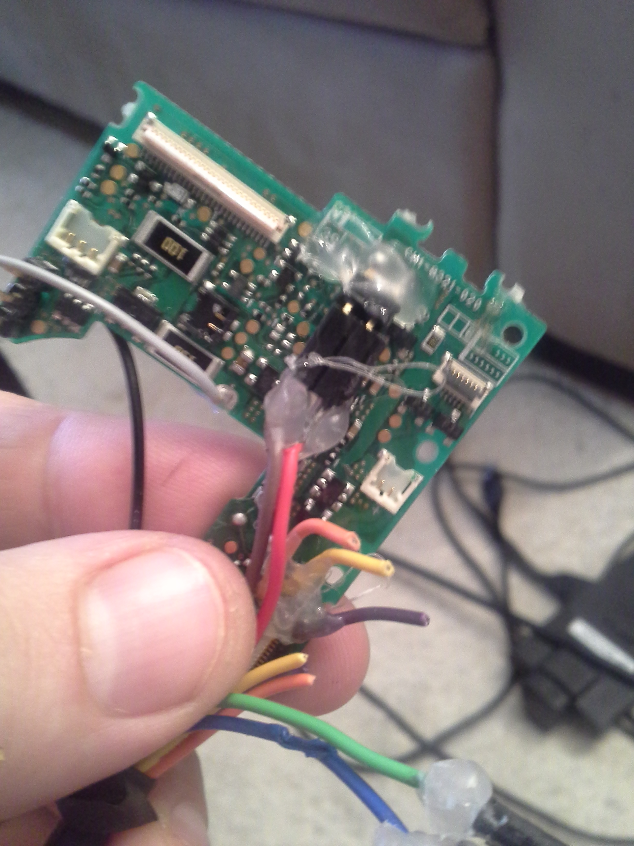
images/assy/2014-08-03 21.07.59.jpg
