varjagg/digital-modul-m/images/assy/2014-08-05 23.45.38.jpg

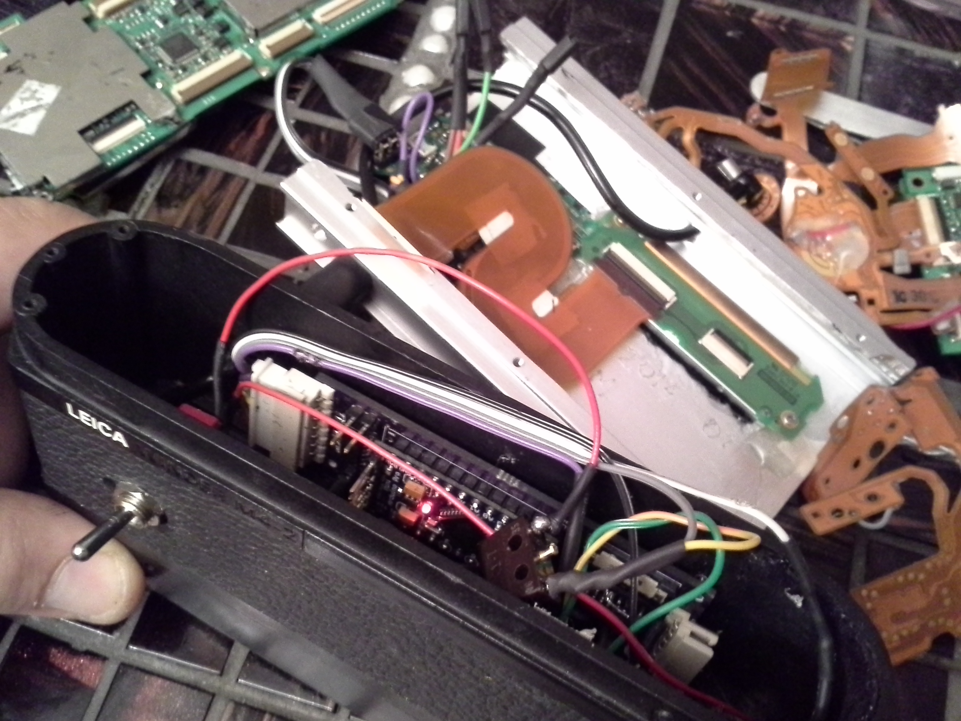
images/assy/2014-08-05 23.45.38.jpg
