varjagg/digital-modul-m/images/assy/2014-08-07 23.46.15.jpg

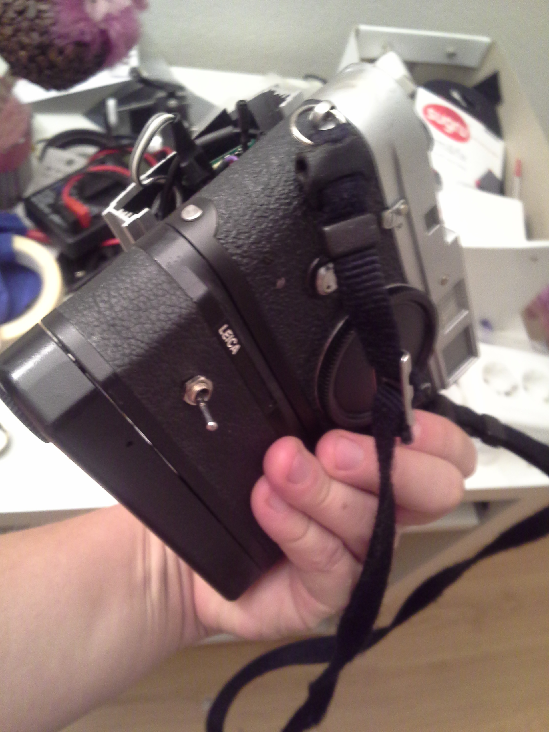
images/assy/2014-08-07 23.46.15.jpg
