varjagg/digital-modul-m/images/assy/2014-08-30 21.43.32.jpg

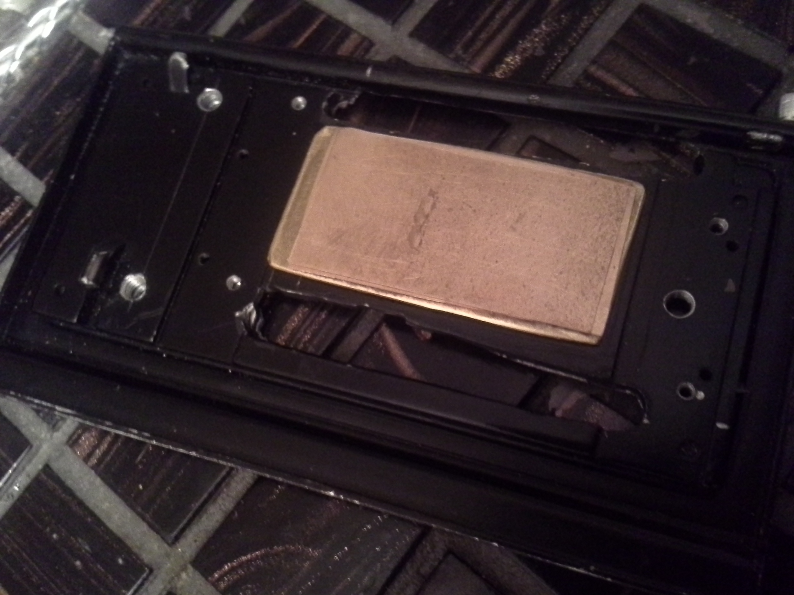
images/assy/2014-08-30 21.43.32.jpg
