varjagg/digital-modul-m/images/assy/2014-08-31 18.50.45.jpg

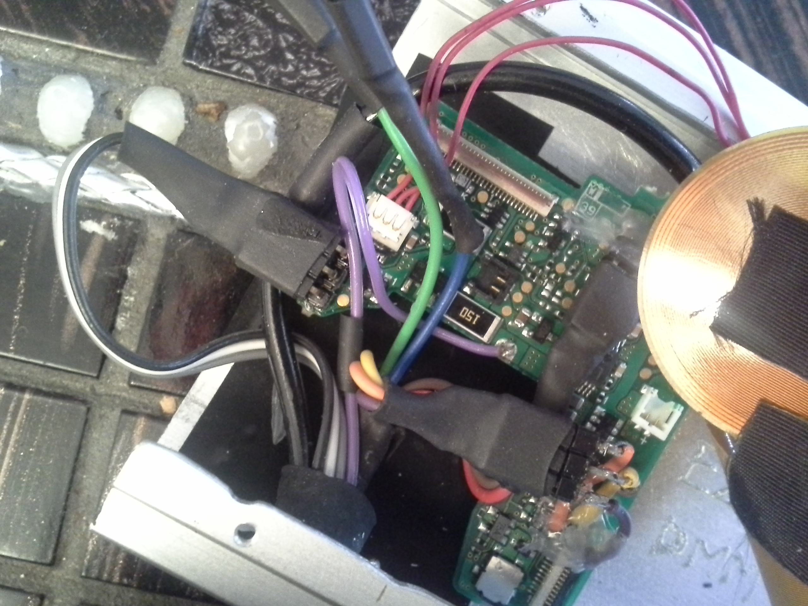
images/assy/2014-08-31 18.50.45.jpg
