varjagg/digital-modul-m/images/assy/2014-08-31 18.51.22.jpg

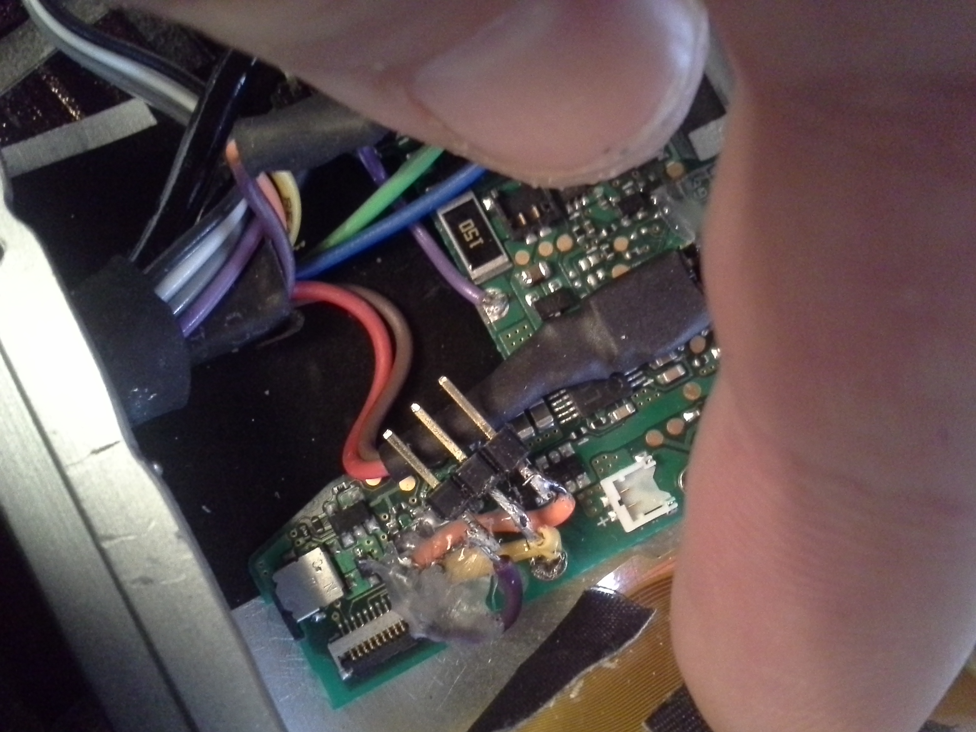
images/assy/2014-08-31 18.51.22.jpg
