varjagg/digital-modul-m/images/assy/shutter_sync_mod.jpg

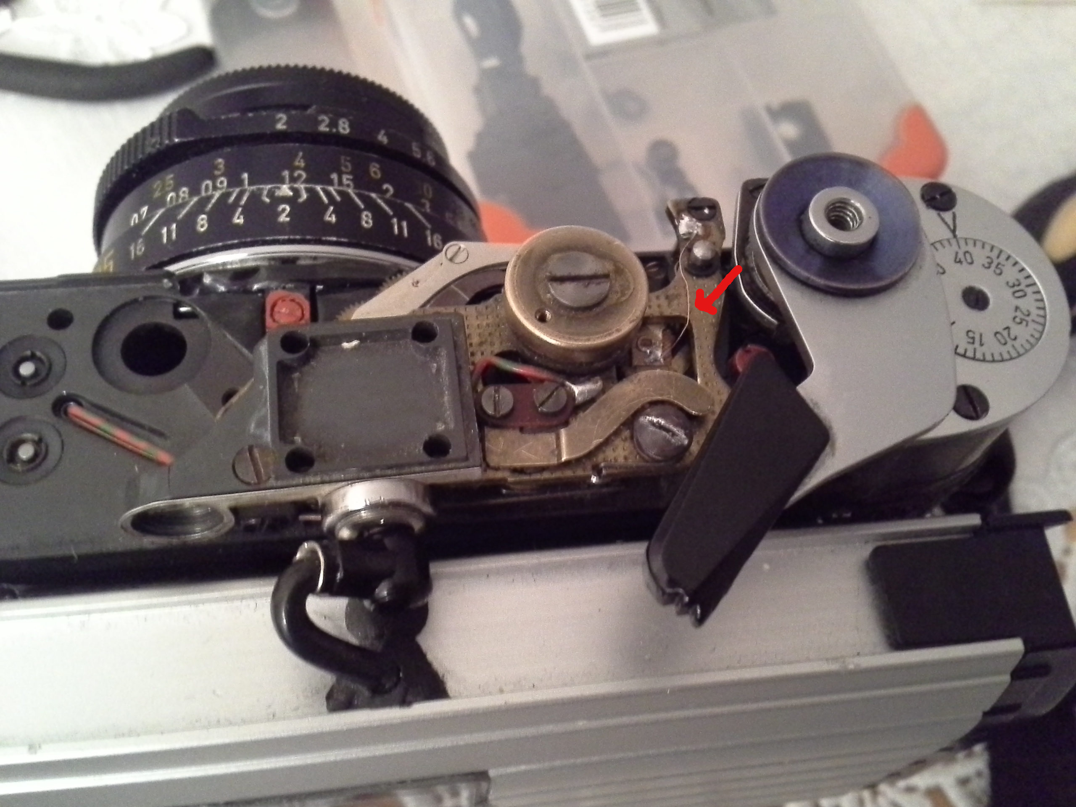
images/assy/shutter_sync_mod.jpg
