varjagg/digital-modul-m/images/mirror_0.5s_fire.png

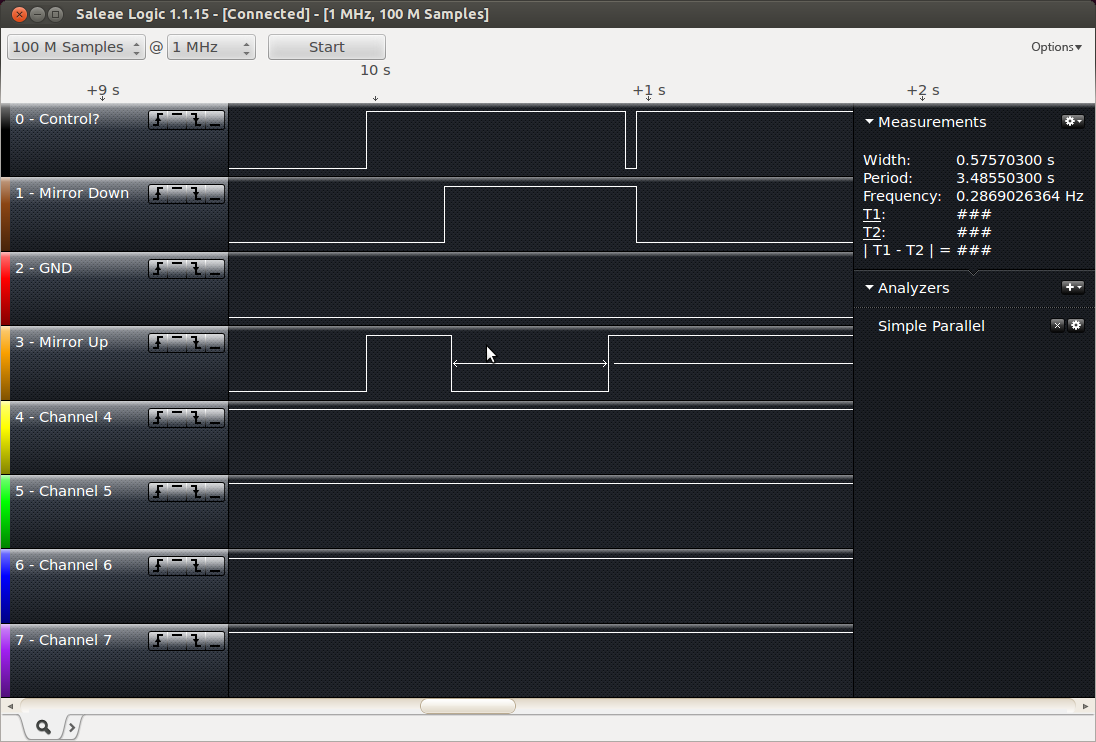
images/mirror_0.5s_fire.png
