varjagg/digital-modul-m/images/mirror_shutter_control_pcb.png

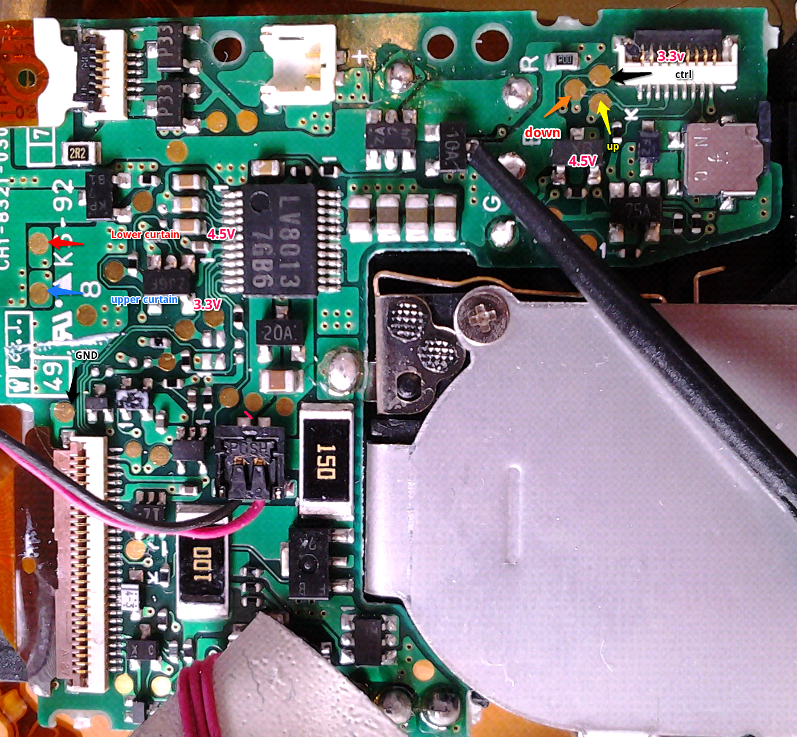
images/mirror_shutter_control_pcb.png
