varjagg/digital-modul-m/images/mystery.png

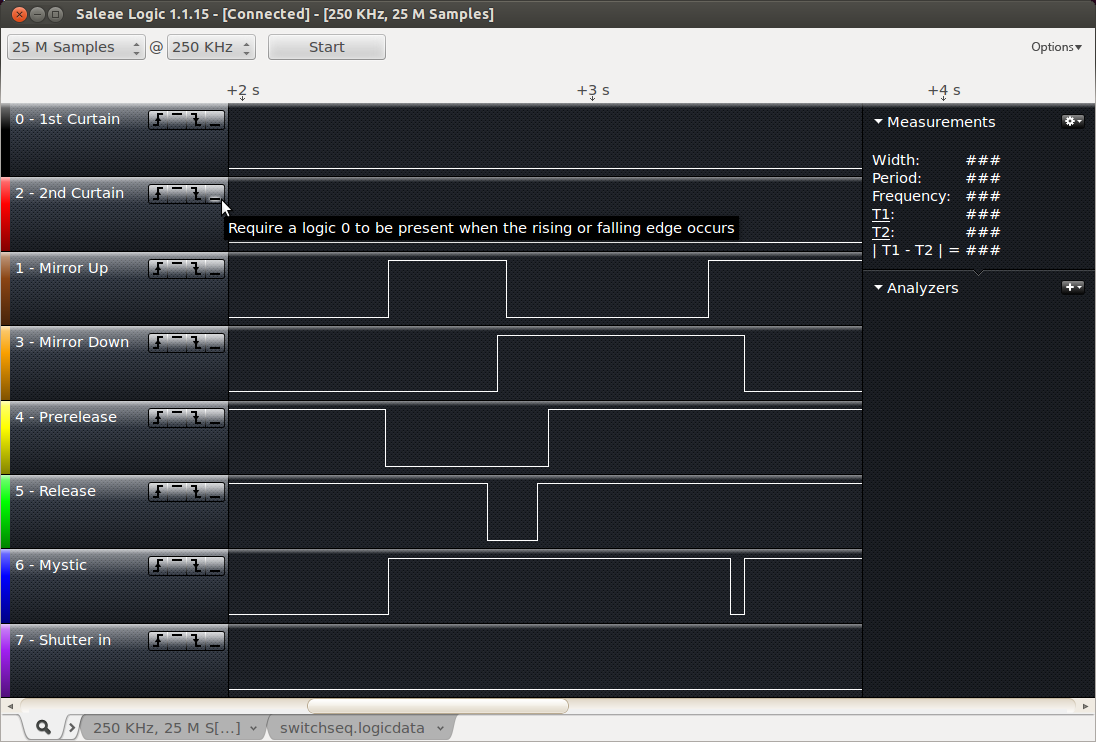
images/mystery.png
