varjagg/digital-modul-m/images/mystic2.png

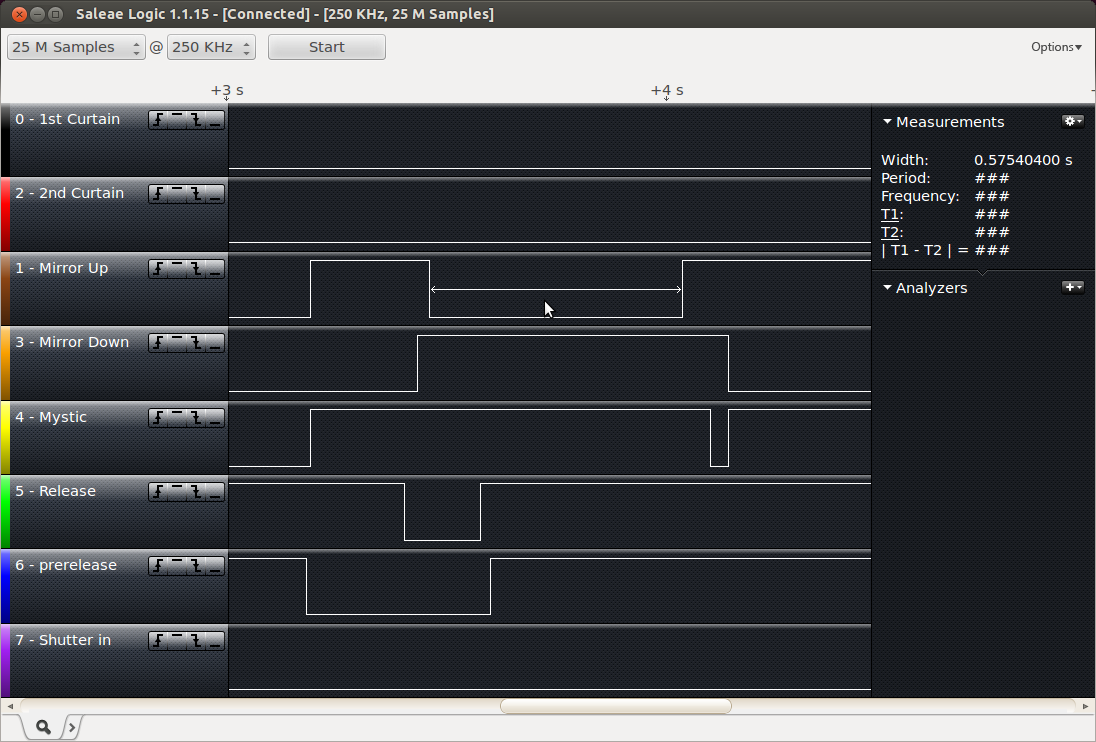
images/mystic2.png
